mark77-DE/Smart-Filament-Sample-Board/screenshots/halter-3d.png

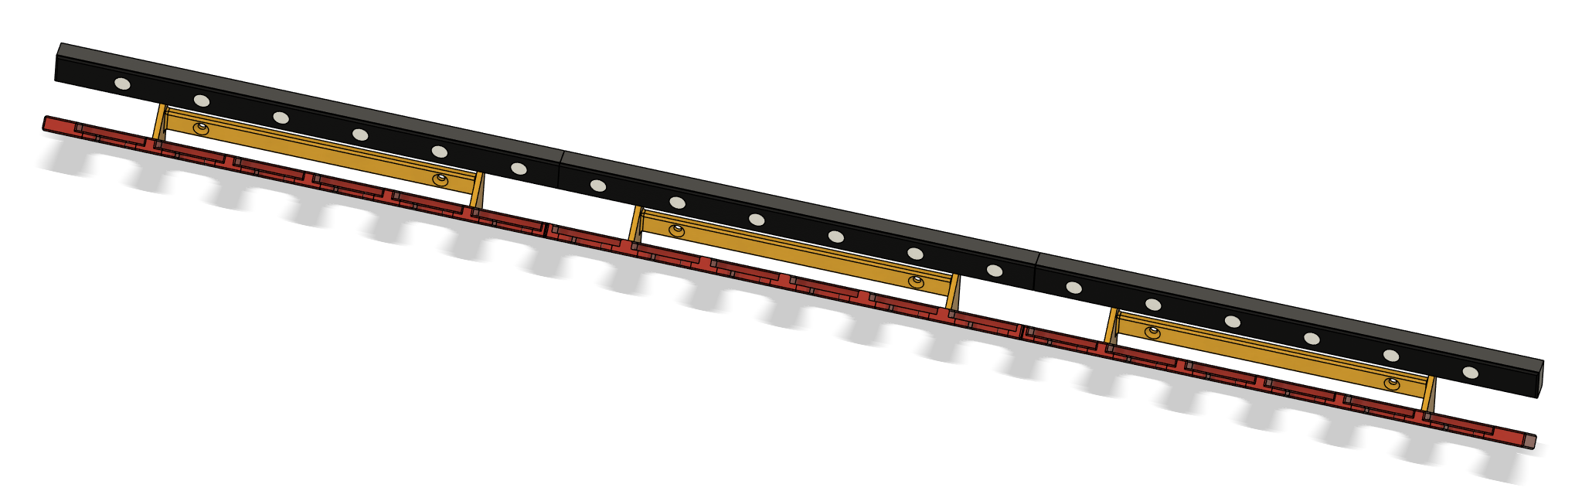
screenshots/halter-3d.png
