mark77-DE/Smart-Filament-Sample-Board/screenshots/samplefuss.png

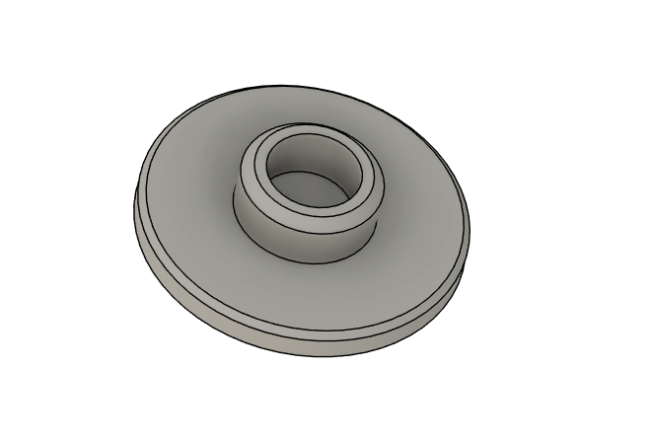
screenshots/samplefuss.png
