mark77-DE/Smart-Filament-Sample-Board/screenshots/settings_button.png

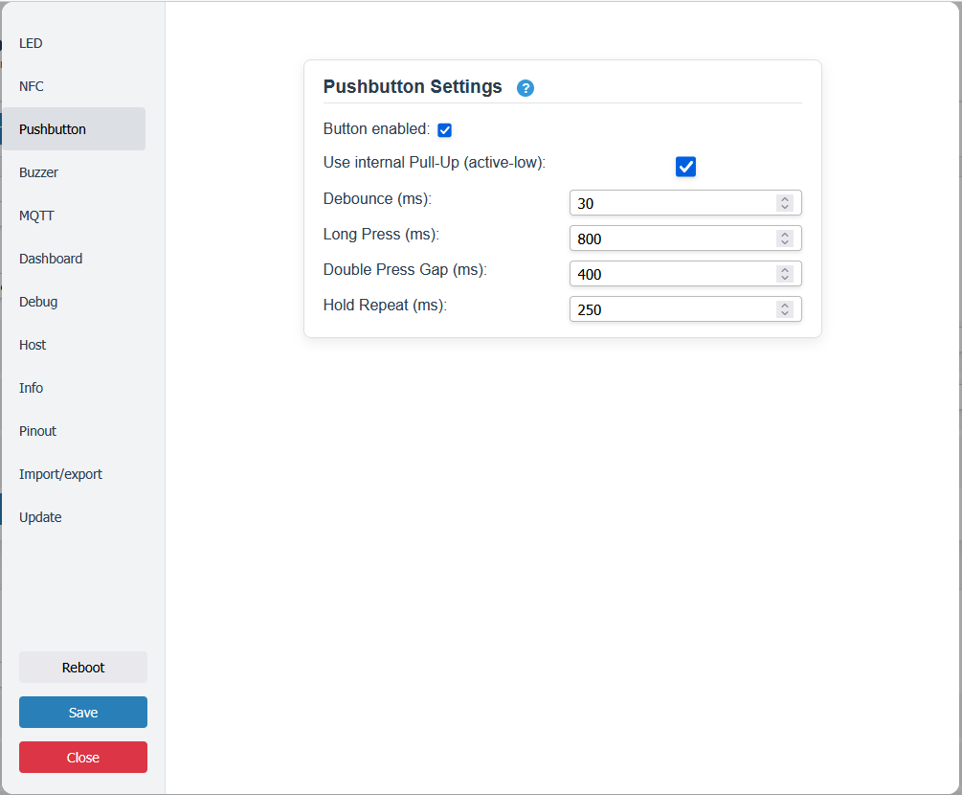
screenshots/settings_button.png
