mark77-DE/Smart-Filament-Sample-Board/screenshots/settings_dashboard.png

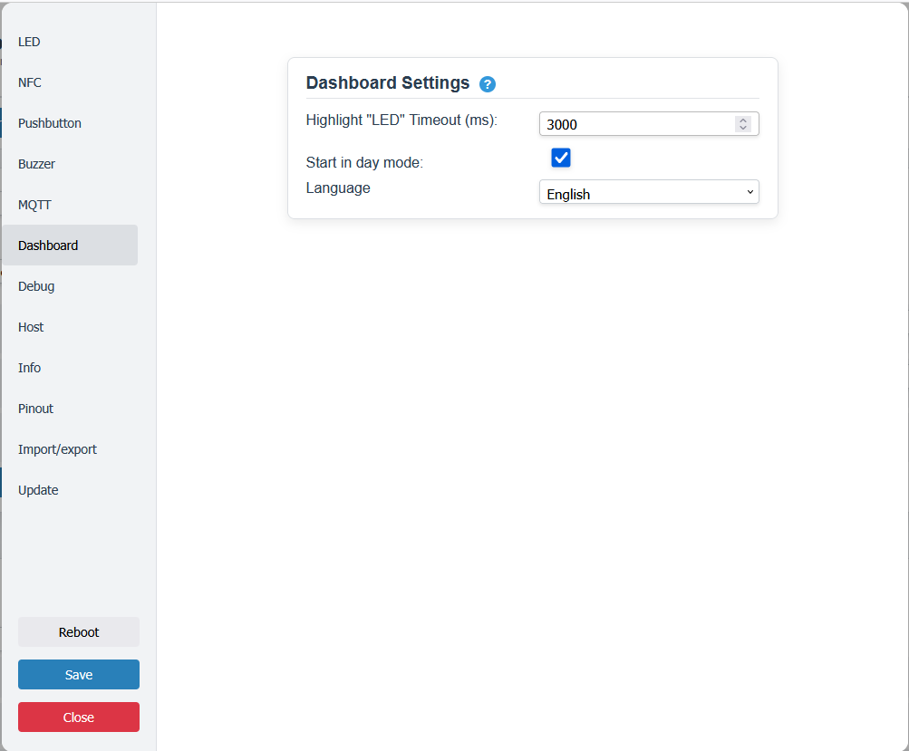
screenshots/settings_dashboard.png
