mark77-DE/Smart-Filament-Sample-Board/screenshots/settings_host.png

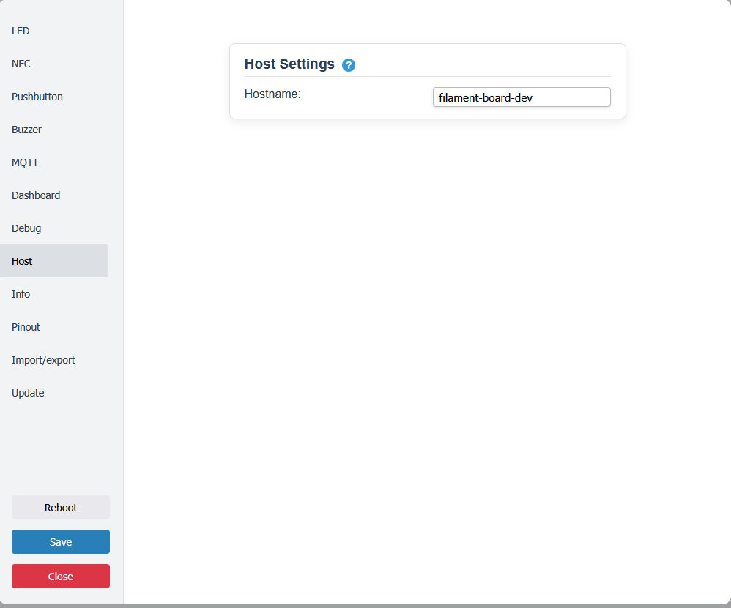
screenshots/settings_host.png
