mark77-DE/Smart-Filament-Sample-Board/screenshots/settings_import-export.png

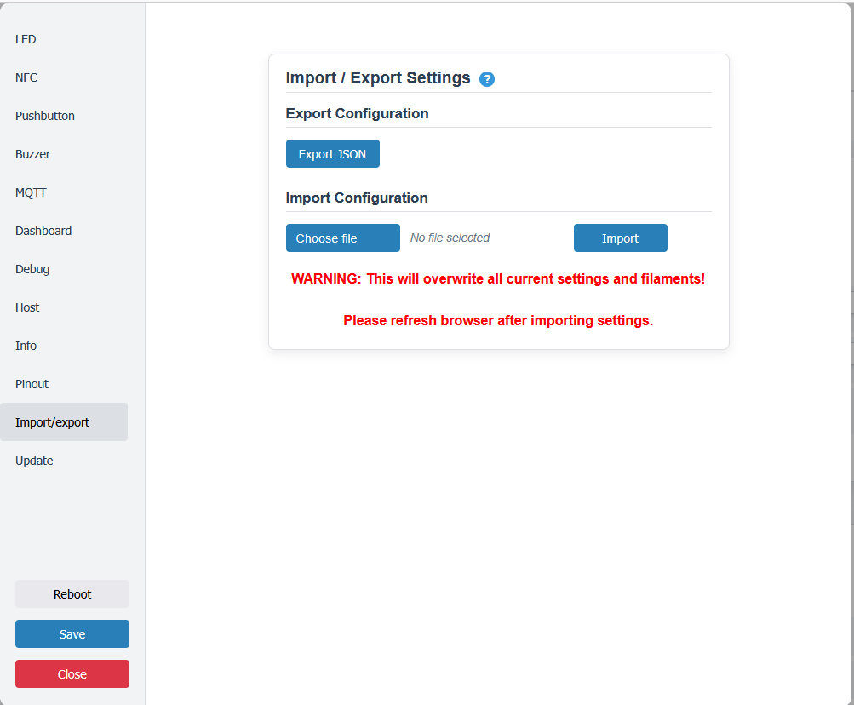
screenshots/settings_import-export.png
