mark77-DE/Smart-Filament-Sample-Board/screenshots/settings_info-1.png

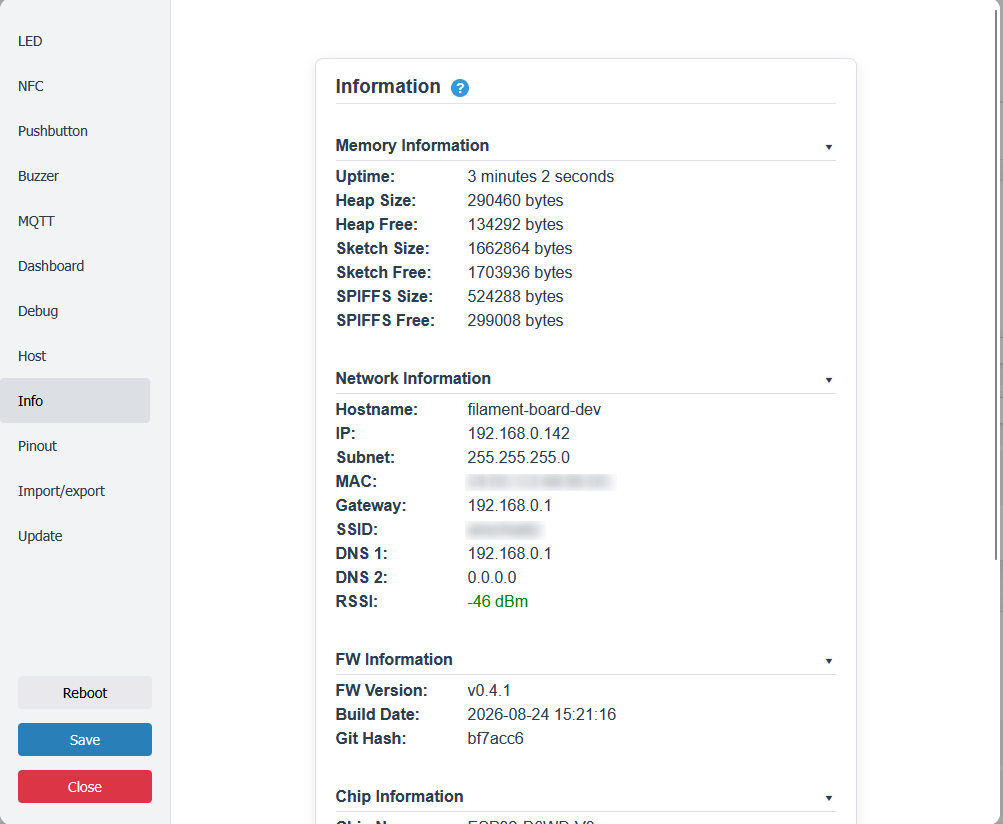
screenshots/settings_info-1.png
