mark77-DE/Smart-Filament-Sample-Board/screenshots/settings_main.png

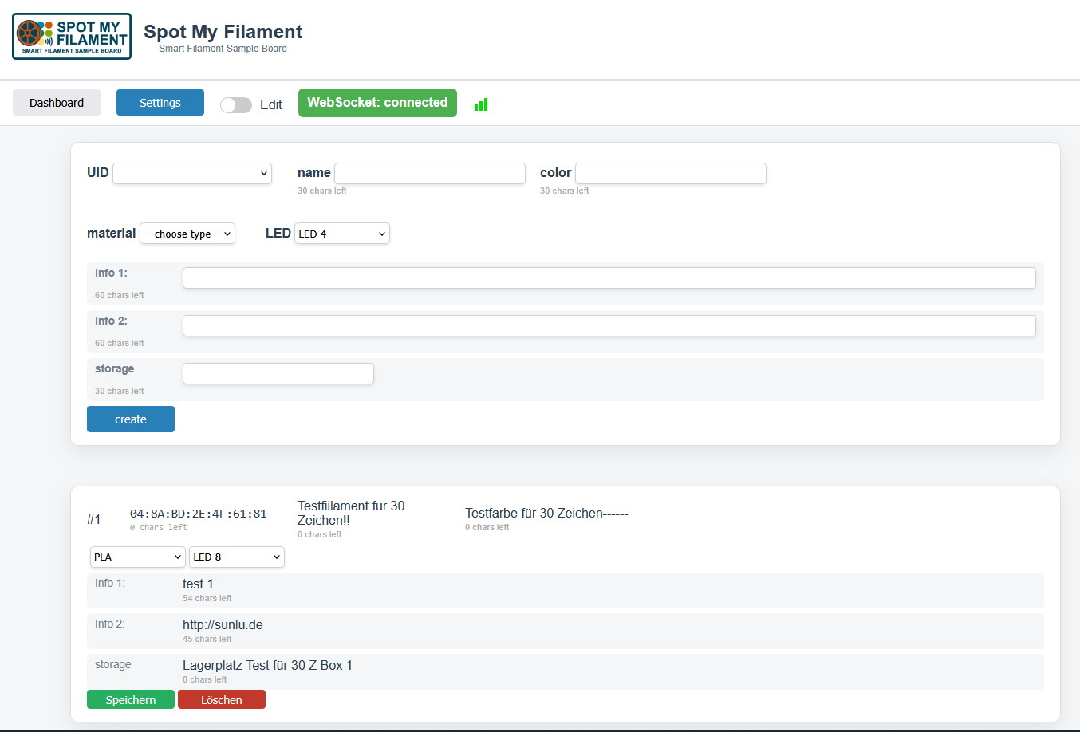
screenshots/settings_main.png
