mark77-DE/Smart-Filament-Sample-Board/screenshots/settings_main_led.png

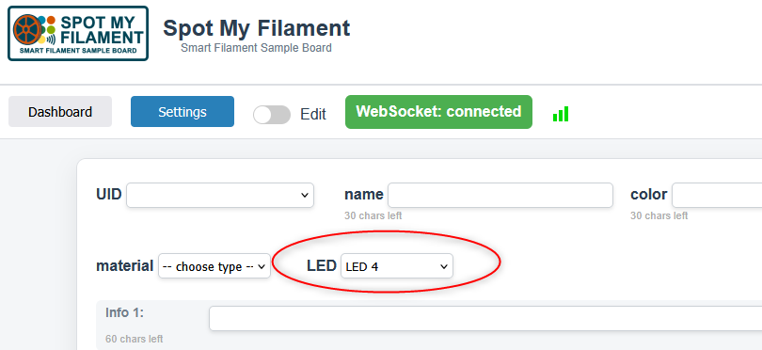
screenshots/settings_main_led.png
