mark77-DE/Smart-Filament-Sample-Board/screenshots/settings_update.png

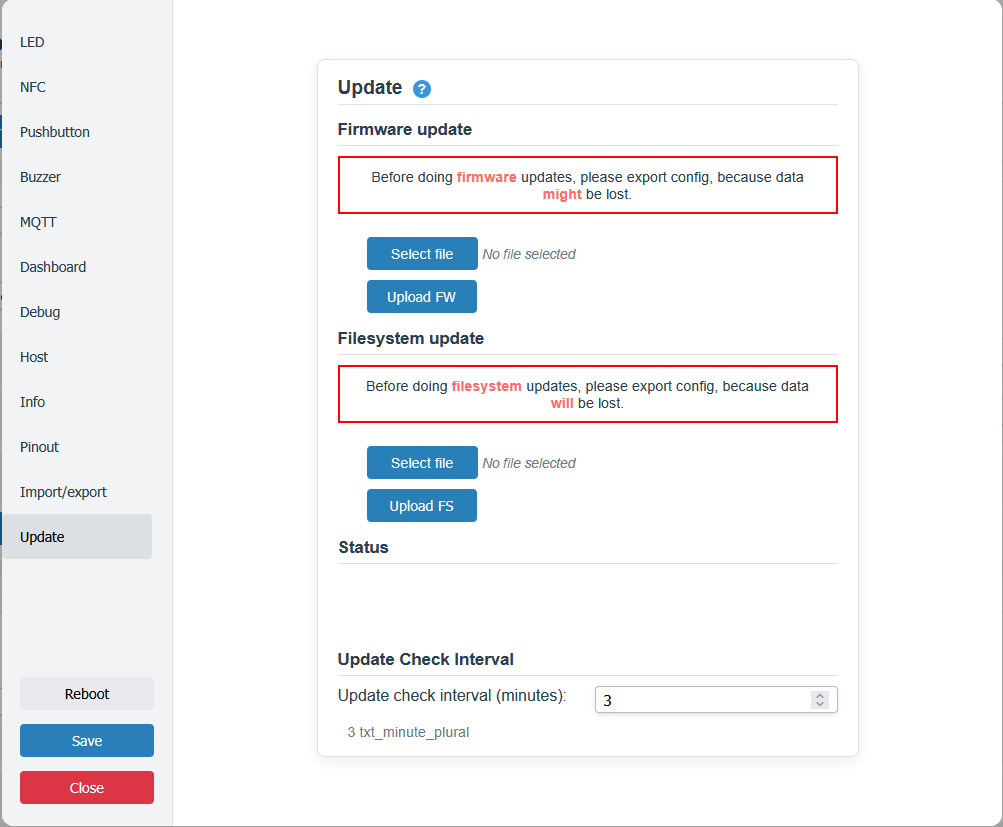
screenshots/settings_update.png
