mark77-DE/Smart-Filament-Sample-Board/3D-Daten/CDU/CDU_Kolja_V3_Wandhalterung_Schrauben.stl

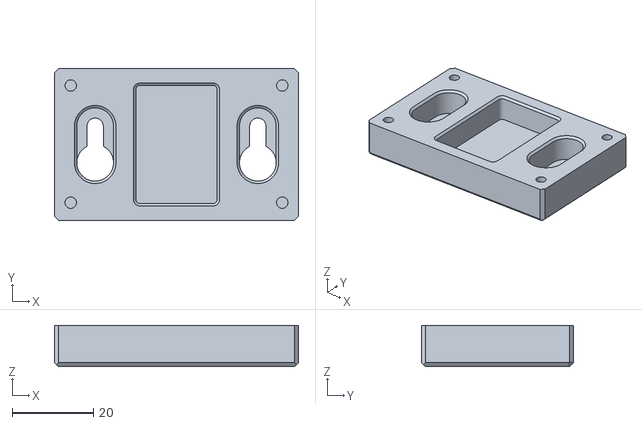
[picture p35: CAD file, 2025-12-17]
3D-Daten/CDU/CDU_Kolja_V3_Wandhalterung_Schrauben.stl
60.0 x 37.3 x 10.2
