mark77-DE/Smart-Filament-Sample-Board/3D-Daten/Printfiles/Filament-Sample-Board_6x.3mf

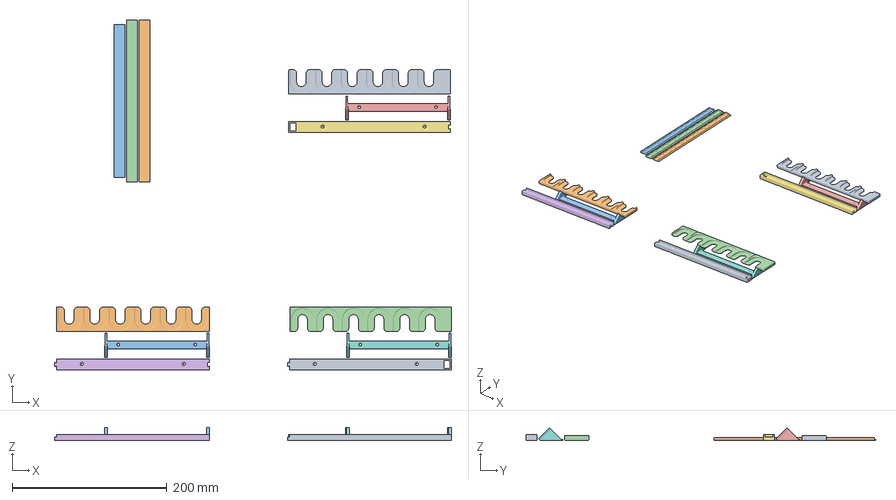
[picture p36: CAD file, 2026-08-30]
3D-Daten/Printfiles/Filament-Sample-Board_6x.3mf
513.6 x 452.6 x 16.2 mm
Sample-Mount_left
Sample-Mount_middle
Wall-mount_middle
Sample-Mount_right
Wall-mount_left
LED-Mount_middle
LED-Mount_left
Wall-mount_right
LED-Mount_right
Left
Middle
Right
