mark77-DE/Smart-Filament-Sample-Board/3D-Daten/CAD-Komponenten/ESP32-C3.step

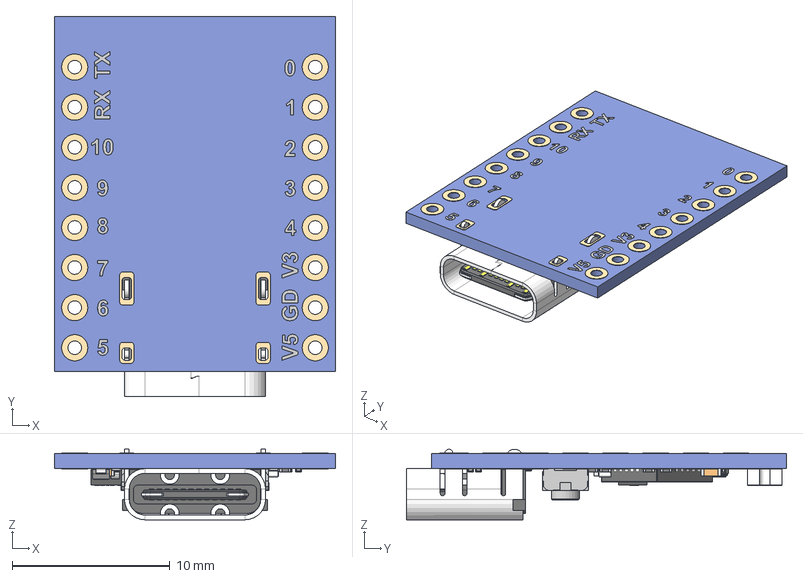
[picture p38: CAD file, 2025-12-13]
3D-Daten/CAD-Komponenten/ESP32-C3.step
17.8 x 24.1 x 4.47 mm
