mark77-DE/Smart-Filament-Sample-Board/3D-Daten/CDU/CDU_Kolja_V3_WAGO_Cover_Mounting_Plate.3mf

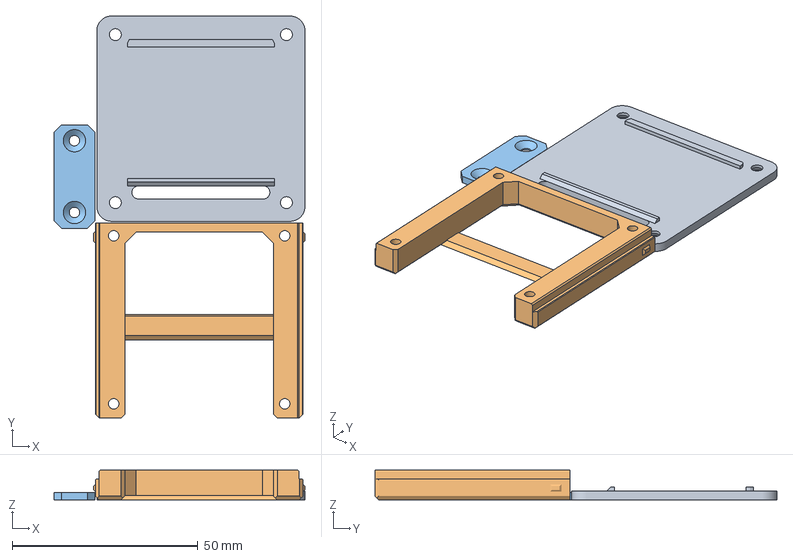
[picture p39: CAD file, 2025-12-17]
3D-Daten/CDU/CDU_Kolja_V3_WAGO_Cover_Mounting_Plate.3mf
67.5 x 108.1 x 8.00 mm
CDU_Kolja_V3_WAGO_Cover_Mounting_Plate.stl
CDU_Kolja_V3_WAGO_Slide_Rail.stl
CDU_Kolja_V3_USB_Cover.stl
