mark77-DE/Smart-Filament-Sample-Board/3D-Daten/Printfiles/Filament-Sample-Board_7x.3mf

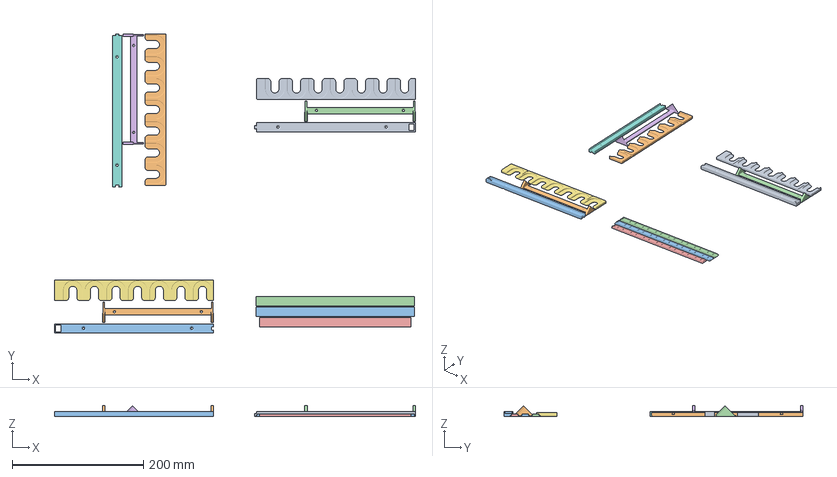
[picture p40: CAD file, 2026-08-30]
3D-Daten/Printfiles/Filament-Sample-Board_7x.3mf
550.7 x 456.6 x 16.2 mm
Sample-Mount_right
Sample-Mount_middle
LED-Cover_left
Wall-Mount_right
LED-Cover_middle
Wall-mount_middle
Sample-Mount_left
LED-Mount_middle
LED-Mount_right
Wall-Mount_left
LED-Mount_left
LED-Cover_right
