mark77-DE/Smart-Filament-Sample-Board/3D-Daten/CAD-Daten_Halter/Alte Version/FilamentSampleRegal v10.step

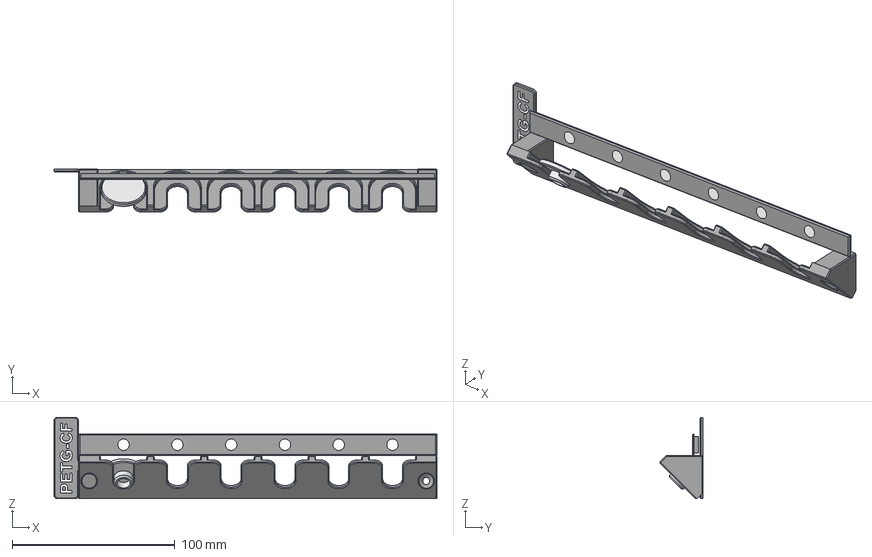
[picture p41: CAD file, 2025-12-06]
3D-Daten/CAD-Daten_Halter/Alte Version/FilamentSampleRegal v10.step
235.0 x 26.4 x 50.0 mm
Halter
LED-Halter-Deckel
SampleFuss
Schild
SchraubenKappe
