mark77-DE/Smart-Filament-Sample-Board/3D-Daten/CAD-Komponenten/OLED 2.42 V1.1 SSD1309.STEP

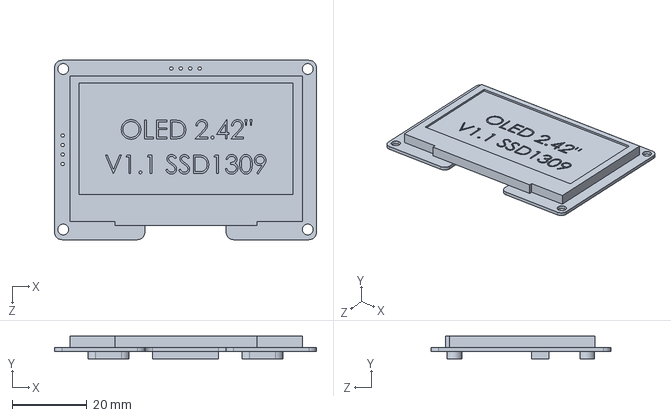
[picture p42: CAD file, 2025-12-13]
3D-Daten/CAD-Komponenten/OLED 2.42 V1.1 SSD1309.STEP
70.2 x 6.10 x 48.1 mm
