mark77-DE/Smart-Filament-Sample-Board/3D-Daten/CDU/CDU_Kolja_V3_NFC_Einsatz.3mf

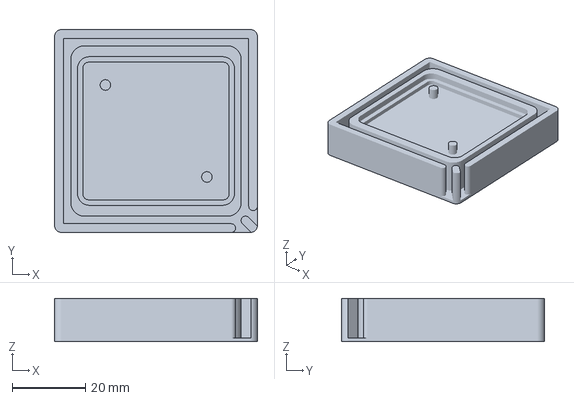
[picture p43: CAD file, 2025-12-17]
3D-Daten/CDU/CDU_Kolja_V3_NFC_Einsatz.3mf
55.6 x 55.6 x 11.8 mm
