mark77-DE/Smart-Filament-Sample-Board/3D-Daten/CAD-Daten_Halter/Alte Version/Halter.step

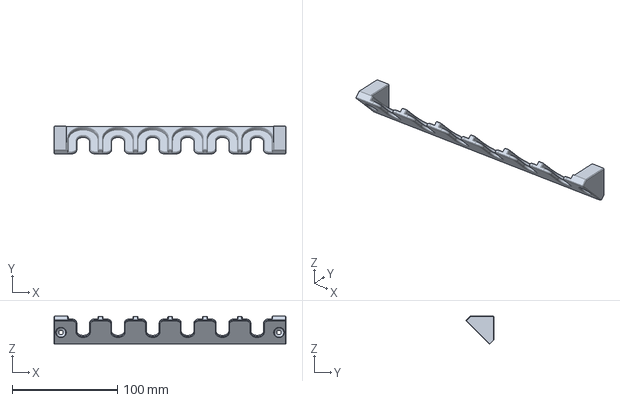
[picture p44: CAD file, 2025-12-06]
3D-Daten/CAD-Daten_Halter/Alte Version/Halter.step
220.0 x 26.4 x 26.4 mm
