mark77-DE/Smart-Filament-Sample-Board/3D-Daten/CAD-Komponenten/221-2411.stp

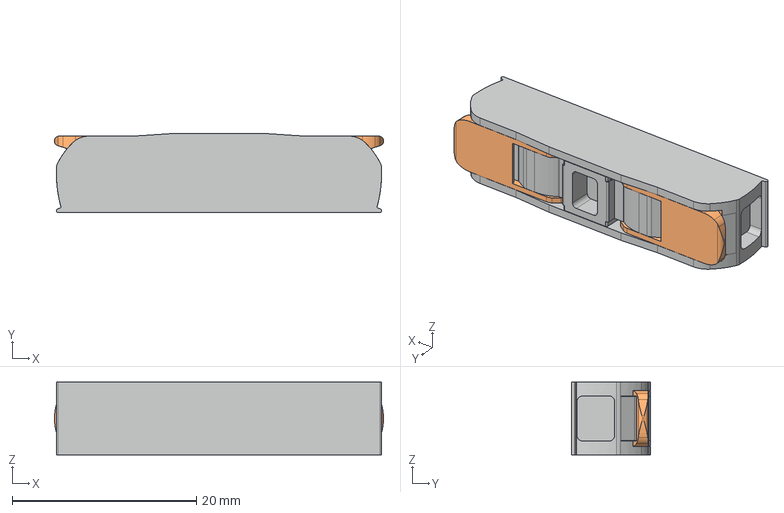
[picture p45: CAD file, 2025-12-13]
3D-Daten/CAD-Komponenten/221-2411.stp
35.7 x 8.60 x 7.90 mm
