mark77-DE/Smart-Filament-Sample-Board/3D-Daten/CDU/CDU_Kolja_V3_Final_Frontplatte.stp

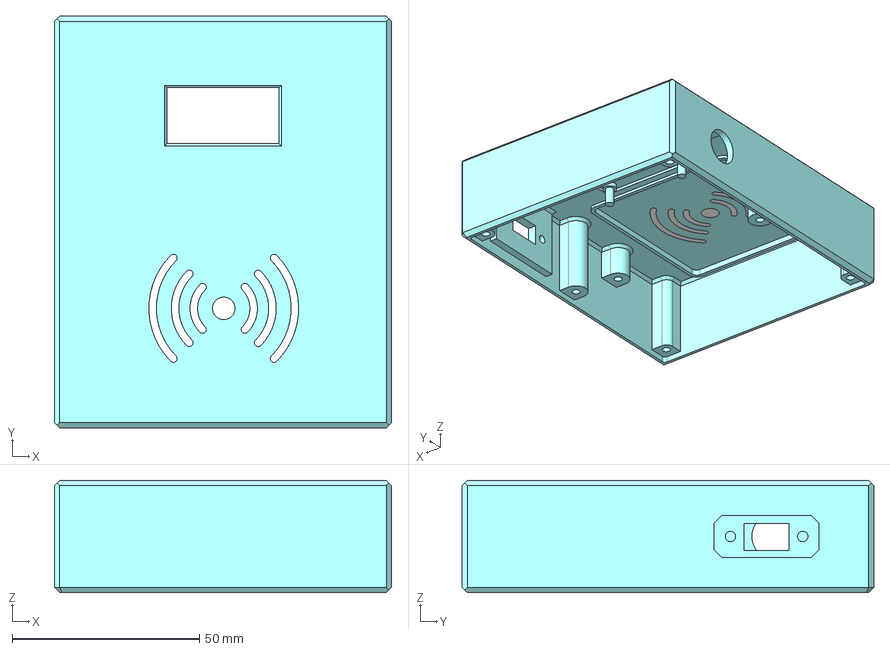
[picture p46: CAD file, 2025-12-17]
3D-Daten/CDU/CDU_Kolja_V3_Final_Frontplatte.stp
90.0 x 110.0 x 30.0 mm
Frontplatte
NFC_Symbol
