mark77-DE/Smart-Filament-Sample-Board/3D-Daten/CAD-Daten_Halter/Alte Version/SampleFuss.step

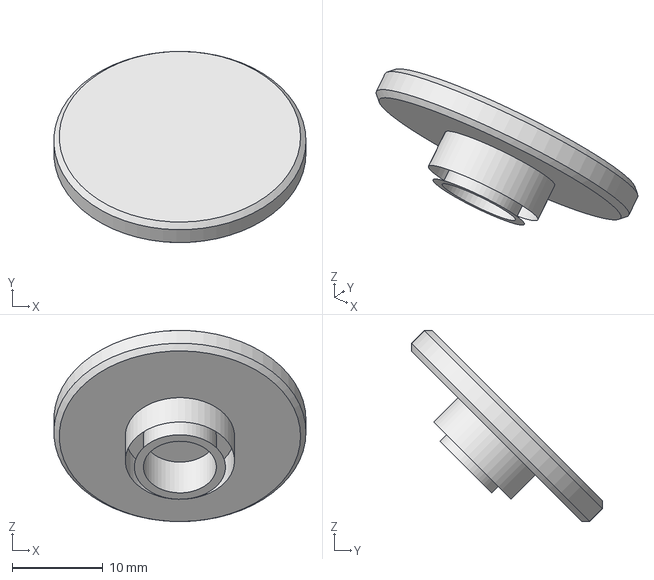
[picture p47: CAD file, 2025-12-06]
3D-Daten/CAD-Daten_Halter/Alte Version/SampleFuss.step
27.8 x 21.1 x 21.1 mm
