mark77-DE/Smart-Filament-Sample-Board/3D-Daten/CAD-Komponenten/Adafruit_NeoPixel_Stick_8.step

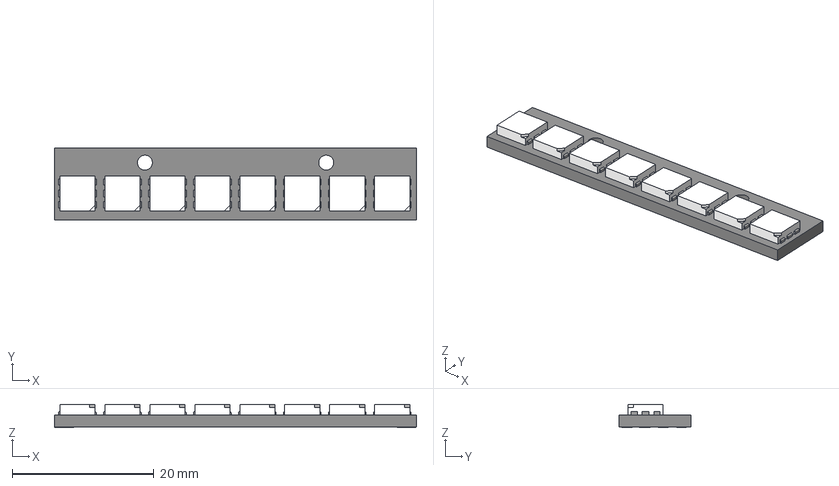
[picture p48: CAD file, 2025-12-13]
3D-Daten/CAD-Komponenten/Adafruit_NeoPixel_Stick_8.step
51.1 x 10.2 x 3.27 mm
NeoPixel Stick - 8 x WS2812 5050 RGB LED v2
LED - SMD RGB (WS2812) x 8
Solder Pads
