mark77-DE/Smart-Filament-Sample-Board/3D-Daten/CDU/CDU_Kolja_V3_Final_ESP32_Plate.stp

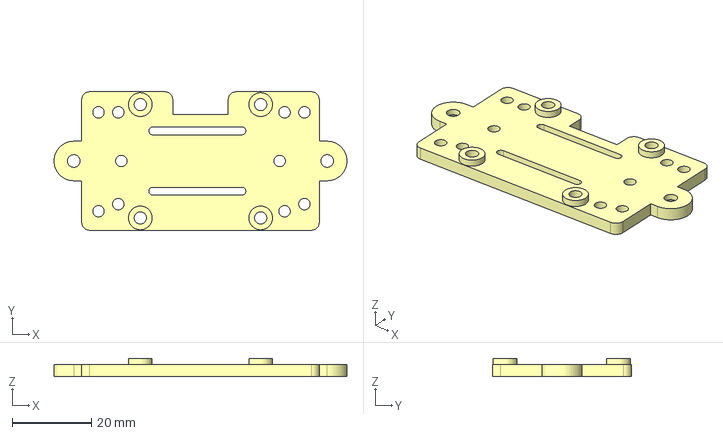
[picture p49: CAD file, 2025-12-17]
3D-Daten/CDU/CDU_Kolja_V3_Final_ESP32_Plate.stp
74.0 x 35.0 x 4.60 mm
ESP_Schrift
ESP_Platte
