mark77-DE/Smart-Filament-Sample-Board/3D-Daten/CAD-Komponenten/OLED13_IIC.stp

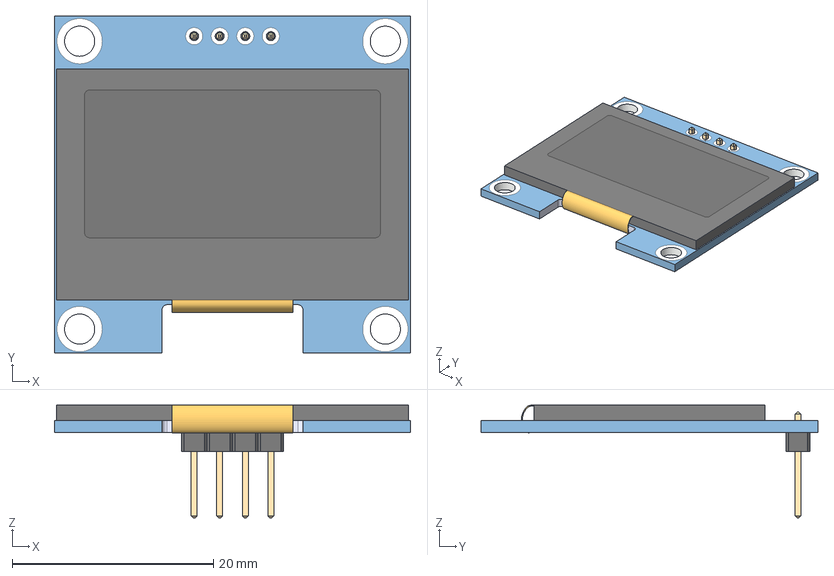
[picture p50: CAD file, 2025-12-13]
3D-Daten/CAD-Komponenten/OLED13_IIC.stp
35.4 x 33.5 x 11.2 mm
