mark77-DE/Smart-Filament-Sample-Board/3D-Daten/CDU/CDU_Kolja_V3_WAGO_Slide_Rail.stl

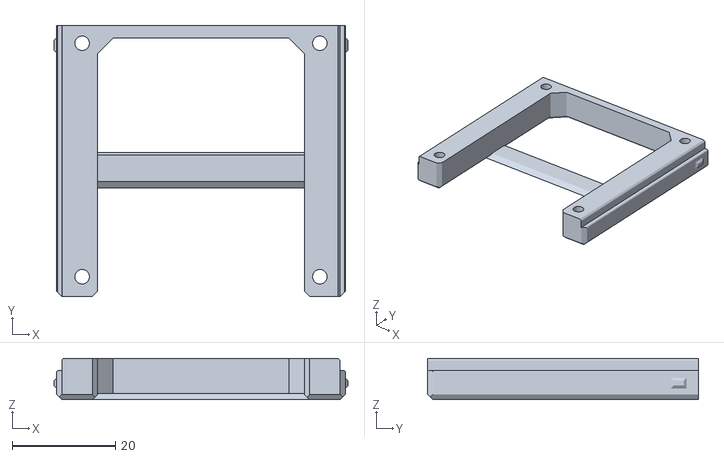
[picture p51: CAD file, 2025-12-17]
3D-Daten/CDU/CDU_Kolja_V3_WAGO_Slide_Rail.stl
56.9 x 52.4 x 8.00
