mark77-DE/Smart-Filament-Sample-Board/3D-Daten/CAD-Daten_Halter/Alte Version/Schild_PLA.step

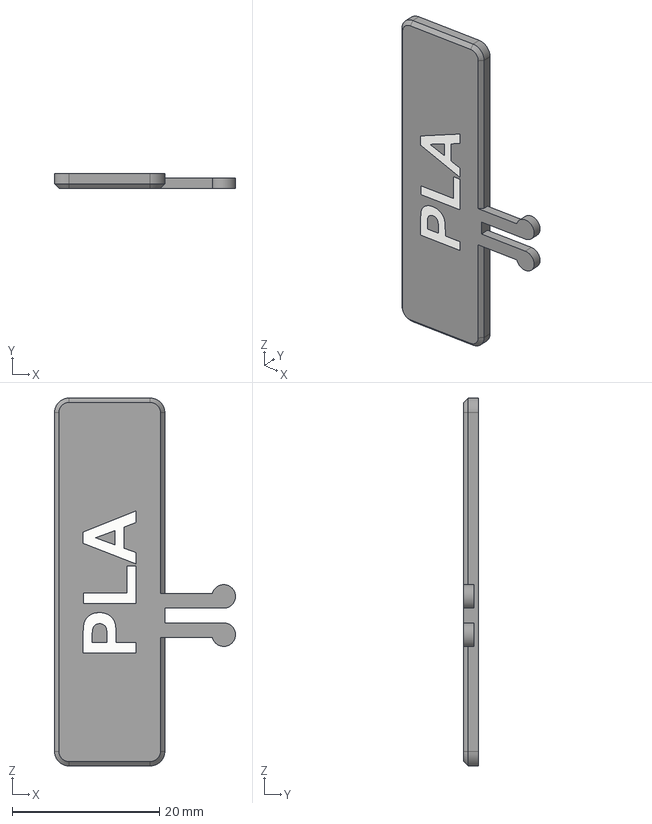
[picture p52: CAD file, 2025-12-06]
3D-Daten/CAD-Daten_Halter/Alte Version/Schild_PLA.step
24.6 x 2.00 x 50.0 mm
