mark77-DE/Smart-Filament-Sample-Board/ESP32-Webserver/src/display/oled/display_anim.cpp

#include "display/display_config.h"

#if DISPLAY_TYPE == DISPLAY_TYPE_SH1106

#include "display/display_anim.h"
#include "display/display.h"
#include "gpio_hardware.h"


// Diese Werte stammen aus dem Animator-Export:
#define FRAME_WIDTH  64
#define FRAME_HEIGHT 64

// Animation
const byte PROGMEM frames[][512] = {
  {0,0,0,0,0,0,0,0,0,0,0,0,0,0,0,0,0,0,0,0,0,0,0,0,0,0,0,0,0,0,0,0,0,0,0,0,0,0,0,0,0,0,0,0,0,0,0,0,0,0,0,0,0,0,0,0,0,0,0,0,0,0,0,0,0,0,0,0,0,0,0,0,0,0,0,0,0,0,0,0,0,0,0,0,0,0,0,0,0,0,0,0,0,0,0,0,0,0,0,24,0,0,0,0,0,0,0,24,0,0,0,0,0,0,0,60,0,0,0,0,0,0,0,60,0,0,0,0,0,0,0,60,0,0,0,0,0,0,0,60,0,0,0,0,0,0,0,60,0,0,0,0,0,0,0,124,0,0,0,0,0,0,0,126,0,0,0,0,0,0,0,110,0,0,0,0,0,0,0,102,0,0,0,0,0,0,0,230,0,0,0,0,0,0,0,230,0,0,0,0,0,0,0,230,0,0,0,0,0,1,192,199,0,96,0,0,0,1,192,199,0,112,0,0,0,3,225,195,0,240,0,0,0,3,225,195,0,248,0,0,0,7,225,131,0,248,0,0,0,7,113,131,1,216,0,0,0,14,115,131,129,220,0,0,7,254,51,131,129,156,31,224,15,252,59,129,131,140,63,240,7,248,63,1,131,142,127,224,0,0,31,1,131,142,96,0,0,0,31,1,131,7,224,0,0,0,15,1,199,7,192,0,0,0,14,1,199,3,192,0,0,0,14,0,198,3,128,0,0,0,6,0,206,1,0,0,0,0,0,0,206,0,0,0,0,0,0,0,204,0,0,0,0,0,0,0,252,0,0,0,0,0,0,0,252,0,0,0,0,0,0,0,120,0,0,0,0,0,0,0,120,0,0,0,0,0,0,0,120,0,0,0,0,0,0,0,112,0,0,0,0,0,0,0,112,0,0,0,0,0,0,0,112,0,0,0,0,0,0,0,0,0,0,0,0,0,0,0,0,0,0,0,0,0,0,0,0,0,0,0,0,0,0,0,0,0,0,0,0,0,0,0,0,0,0,0,0,0,0,0,0,0,0,0,0,0,0,0,0,0,0,0,0,0,0,0,0,0,0,0,0,0,0,0,0,0,0,0,0,0,0,0,0,0,0,0,0,0,0,0,0,0,0,0,0,0,0,0,0,0,0,0},
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

enum IdleState {
    IDLE_OFF,
    IDLE_ANIM,
    IDLE_TEXT
};

IdleState     s_state          = IDLE_OFF;
uint16_t      s_frame          = 0;
unsigned long s_lastFrameTime  = 0;
unsigned long s_textStartTime  = 0;

// --- Textanimation ---
static const uint8_t MAX_IDLE_TEXT_LEN = 32;

char           s_textBuffer[MAX_IDLE_TEXT_LEN + 1] = {0};
uint8_t        s_textLen         = 0;
uint8_t        s_textCharIndex   = 0;
unsigned long  s_lastCharTime    = 0;

// --- Cursoranimation ---
bool           s_cursorVisible   = false;
unsigned long  s_lastCursorBlink = 0;

// --- Cursor layout (so only the cursor needs to be drawn) ---
bool           s_layoutReady     = false;
int16_t        s_textX           = 0;
int16_t        s_textY           = 0;
uint16_t       s_textW           = 0;
uint16_t       s_textH           = 0;

int16_t        s_cursorX         = 0;
int16_t        s_cursorY         = 0;
uint16_t       s_cursorW         = 0;
uint16_t       s_cursorH         = 0;

static int16_t s_cursorX1 = 0;   // x-offset aus getTextBounds
static int16_t s_cursorY1 = 0;   // y-offset aus getTextBounds

// ------------------------------------------------------------
// Frame cropping for 32px
// ------------------------------------------------------------

static void drawFrameCropped(DisplayType &display, uint16_t frameIdx) {
    // 1bpp Bitmap: bytes pro Zeile
    const int16_t bytesPerRow = (FRAME_WIDTH + 7) / 8;

    // Target height = min(FRAME_HEIGHT, SCREEN_HEIGHT)
    int16_t drawH = FRAME_HEIGHT;
    if (SCREEN_HEIGHT < FRAME_HEIGHT) drawH = SCREEN_HEIGHT;

    // Vertikal mittig aus dem 64px Frame ausschneiden
    int16_t srcYOffset = 0;
        if (drawH < FRAME_HEIGHT) {
        #if FRAME_CROP_MODE_CENTER
            srcYOffset = (FRAME_HEIGHT - drawH) / 2;
        #else
        srcYOffset = 0; // oben abschneiden
        #endif
}


    const uint8_t* bmp = &frames[frameIdx][0];
    bmp += srcYOffset * bytesPerRow; // vertikal „croppen“

    int16_t x = (SCREEN_WIDTH  - FRAME_WIDTH) / 2;
    int16_t y = (SCREEN_HEIGHT - drawH)      / 2;
    if (x < 0) x = 0;
    if (y < 0) y = 0;

    displayClear();
    display.drawBitmap(x, y, bmp, FRAME_WIDTH, drawH, DISPLAY_COLOR);
    displayFlush();
}


// ------------------------------------------------------------
// Reset animation
// ------------------------------------------------------------
static void resetTextAnimation(unsigned long now) {
    const char *src = IDLE_TEXT_STRING;
    size_t len = strlen(src);
    if (len > MAX_IDLE_TEXT_LEN) len = MAX_IDLE_TEXT_LEN;

    memcpy(s_textBuffer, src, len);
    s_textBuffer[len] = '\0';

    s_textLen         = len;
    s_textCharIndex   = 0;
    s_lastCharTime    = 0;

    s_cursorVisible   = false;
    s_lastCursorBlink = 0;

    s_textStartTime   = now;

    s_layoutReady     = false;   // Layout will be calculated later
}


// ------------------------------------------------------------
// Helper: draw centered text (for typing phase)
// (still clears the display, but only while typing)
// ------------------------------------------------------------
static void drawIdleText(DisplayType &display, uint8_t count, bool showCursor) {
    if (count == 0) {
        displayClear();
        displayFlush();
        return;
    }

    if (count > s_textLen)
        count = s_textLen;

    char tmp[MAX_IDLE_TEXT_LEN + 2];

    memcpy(tmp, s_textBuffer, count);
    uint8_t len = count;

    if (showCursor && count == s_textLen) {
        tmp[len++] = '_';
    }

    tmp[len] = '\0';

    int16_t x1, y1;
    uint16_t w, h;

    displayClear();
    display.setTextWrap(false);
    display.setTextColor(DISPLAY_COLOR);

    display.getTextBounds(tmp, 0, 0, &x1, &y1, &w, &h);

    int16_t x = (SCREEN_WIDTH  - (int16_t)w) / 2 - x1;
    int16_t y = (SCREEN_HEIGHT - (int16_t)h) / 2 - y1;

    if (x < 0) x = 0;
    if (y < 0) y = 0;

    display.setCursor(x, y);
    display.print(tmp);
    displayFlush();
}


// ------------------------------------------------------------
// Calculate layout for text + cursor (without clearing anything)
// ------------------------------------------------------------
static void computeLayout(DisplayType &display) {
    if (s_layoutReady || s_textLen == 0) return;

    int16_t x1, y1;
    uint16_t wText, hText;


    // Nur den finalen Text vermessen
    display.getTextBounds(s_textBuffer, 0, 0, &x1, &y1, &wText, &hText);

    int16_t x = (SCREEN_WIDTH  - (int16_t)wText) / 2 - x1;
    int16_t y = (SCREEN_HEIGHT - (int16_t)hText) / 2 - y1;

    if (x < 0) x = 0;
    if (y < 0) y = 0;

    s_textX = x;
    s_textY = y;
    s_textW = wText;
    s_textH = hText;

    // Determine cursor width/height
    int16_t cx1, cy1;
    uint16_t cw, ch;
    display.getTextBounds("_", 0, 0, &cx1, &cy1, &cw, &ch);

    s_cursorX1 = cx1;
    s_cursorY1 = cy1;

    // Cursor zentriert auf neuer Zeile unter dem Text
    s_cursorX = (SCREEN_WIDTH - cw) / 2;
    s_cursorY = s_textY + s_textH + 4;   // +4 als Abstand nach unten

    // Clamp, damit Cursor immer im sichtbaren Bereich bleibt
    if (s_cursorY + (int16_t)ch > SCREEN_HEIGHT) {
        s_cursorY = SCREEN_HEIGHT - (int16_t)ch;
    }
    if (s_cursorY < 0) s_cursorY = 0;

    s_cursorW = cw;
    s_cursorH = ch;

    s_layoutReady = true;
}


// ------------------------------------------------------------
// Draw/erase only the cursor (no clearDisplay!)
// ------------------------------------------------------------
static void drawCursor(DisplayType &display, bool visible) {
    if (!s_layoutReady) return;

    // Clear the cursor area
    display.fillRect(s_cursorX, s_cursorY, s_cursorW, s_cursorH, 0);

    if (visible) {
        display.setTextWrap(false);
        display.setTextColor(DISPLAY_COLOR);

        // ✅ Baseline-Korrektur (DAS war der Bug!)
        display.setCursor(
            s_cursorX - s_cursorX1,
            s_cursorY - s_cursorY1
        );
        display.print("_");
    }

    displayFlush();
}


} // Ende anonymer Namespace




// ============================================================
// PUBLIC API – NAMESPACE DisplayAnim
// ============================================================

namespace DisplayAnim {


// ------------------------------------------------------------
// Start idle normally → animation first
// ------------------------------------------------------------
void startIdle(unsigned long now) {
    s_state         = IDLE_ANIM;
    s_frame         = 0;
    s_lastFrameTime = 0;

    resetTextAnimation(now);
}


// ------------------------------------------------------------
// Start idle with text -> text first (for boot)
// ------------------------------------------------------------
void startIdleTextFirst(unsigned long now) {
    s_state         = IDLE_TEXT;
    s_frame         = 0;
    s_lastFrameTime = 0;

    resetTextAnimation(now);
}


// ------------------------------------------------------------
// Idle stoppen
// ------------------------------------------------------------
void stop() {
    s_state = IDLE_OFF;
}



// ------------------------------------------------------------
// Haupt-Statemachine
// ------------------------------------------------------------
void tickIdle(DisplayType &display, unsigned long now) {

    switch (s_state) {

        // --------------------------
        case IDLE_OFF:
            return;


        // --------------------------
        case IDLE_ANIM: {
            if (s_lastFrameTime == 0 || (now - s_lastFrameTime) >= IDLE_ANIM_FRAME_DELAY) {

                drawFrameCropped(display, s_frame);

                s_lastFrameTime = now;
                s_frame++;

                if (s_frame >= FRAME_COUNT) {
                    s_state = IDLE_TEXT;
                    resetTextAnimation(now);
                }
            }
        } break;


        // --------------------------
        case IDLE_TEXT: {

            // ===== Typewriter animation (character by character) =====
            if (s_textCharIndex < s_textLen) {

                if (s_lastCharTime == 0) {
                    // first character
                    s_textCharIndex = 1;
                    s_lastCharTime  = now;
                    drawIdleText(display, s_textCharIndex, false);
                }
                else if ((now - s_lastCharTime) >= IDLE_TEXT_CHAR_DELAY) {
                    // Next character
                    s_textCharIndex++;
                    s_lastCharTime = now;
                    drawIdleText(display, s_textCharIndex, false);
                }

                // Layout is needed only when the text is finished
            }

            // ===== Cursor-Blinken, nachdem der Text komplett ist =====
            else {
                // Einmal Layout berechnen (Position von Text & Cursor)
                if (!s_layoutReady) {
                    computeLayout(display);
                    s_cursorVisible   = false;
                    s_lastCursorBlink = now;
                    // Text steht bereits vom letzten drawIdleText()
                }

                if ((now - s_lastCursorBlink) >= IDLE_TEXT_CURSOR_BLINK_INTERVAL) {
                    s_cursorVisible   = !s_cursorVisible;
                    s_lastCursorBlink = now;
                    drawCursor(display, s_cursorVisible);
                }
            }

            // ===== Total duration expired? → return to animation =====
            if ((now - s_textStartTime) >= IDLE_TEXT_DURATION) {
                s_state         = IDLE_ANIM;
                s_frame         = 0;
                s_lastFrameTime = 0;
            }

        } break;

    }
}


// ----------------------------------------------
// 3-line typewriter including backward erasing
// ----------------------------------------------
namespace {

// small helper like in display.cpp
static String fixUmlauts_local(String s) {
    s.replace("ä","ae"); s.replace("ö","oe"); s.replace("ü","ue");
    s.replace("Ä","Ae"); s.replace("Ö","Oe"); s.replace("Ü","Ue");
    s.replace("ß","ss");
    return s;
}

// Draw a centered text snippet at the specified line top
static void drawCenteredSubstringAtTop(
    DisplayType& display,
    const String& full,
    size_t count,
    int16_t yTop
) {
    String s = fixUmlauts_local(full.substring(0, count));
    int16_t x1, y1; uint16_t w, h;
    display.getTextBounds(s, 0, 0, &x1, &y1, &w, &h);
    int16_t x = (int16_t)((SCREEN_WIDTH - (int16_t)w) / 2) - x1;
    int16_t y = (int16_t)(yTop - y1); // yTop ist die "Top"-Kante der Zeile
    display.setCursor(x, y);
    display.print(s);
}

// Layout: determine stable Y top positions for the 3 lines,
// so nothing jitters vertically while typing/deleting.
static void computeThreeLineLayout(
    DisplayType& display,
    int16_t& yTop1,
    int16_t& yTop2,
    int16_t& yTop3
) {
    // Font setzen wie im restlichen UI
    display.setTextWrap(false);
    display.setTextColor(DISPLAY_COLOR);
    display.setTextSize(1);
    display.setFont(DISPLAY_FONT); // darf nullptr sein -> Standardfont

    // Measure reference height (stable)
    int16_t rx1, ry1; uint16_t rw, rh;
    display.getTextBounds("Hg", 0, 0, &rx1, &ry1, &rw, &rh);
    int16_t lineHeight = (int16_t)rh + 2;

    // Total block height (3 lines)
    int16_t totalH = (int16_t)(3 * lineHeight);

    // Choose the top start so the block is vertically centered
    int16_t blockTop = (int16_t)((SCREEN_HEIGHT - totalH) / 2);

    yTop1 = blockTop;
    yTop2 = (int16_t)(blockTop + lineHeight);
    yTop3 = (int16_t)(blockTop + 2 * lineHeight);
}

static inline void delay_with_yield(uint32_t ms) {
    uint32_t until = millis() + ms;
    while ((int32_t)(millis() - until) < 0) { yield(); }
}

} // anonymous namespace


// String-Overload: eigentliche Logik
void playThreeLineTypewriter(
    DisplayType& display,
    const String& line1,
    const String& line2,
    const String& line3,
    uint32_t charDelayMs,
    uint32_t linePauseMs,
    uint32_t endHoldMs,
    bool     eraseBackwards,
    uint32_t eraseCharDelayMs,
    uint32_t eraseLinePauseMs
) {
    // Fix for umlauts (as used in the UI)
    String L1 = fixUmlauts_local(line1);
    String L2 = fixUmlauts_local(line2);
    String L3 = fixUmlauts_local(line3);

    // Stabiles Layout (Y-Positionen)
    int16_t yTop1, yTop2, yTop3;
    computeThreeLineLayout(display, yTop1, yTop2, yTop3);

    auto drawAll = [&](size_t c1, size_t c2, size_t c3) {
        displayClear();
        if (c1) drawCenteredSubstringAtTop(display, L1, c1, yTop1);
        if (c2) drawCenteredSubstringAtTop(display, L2, c2, yTop2);
        if (c3) drawCenteredSubstringAtTop(display, L3, c3, yTop3);
        displayFlush();
    };

    // 1) Type line 1
    for (size_t i = 1; i <= L1.length(); ++i) {
        drawAll(i, 0, 0);
        delay_with_yield(charDelayMs);
    }
    delay_with_yield(linePauseMs);

    // 2) Type line 2
    for (size_t i = 1; i <= L2.length(); ++i) {
        drawAll(L1.length(), i, 0);
        delay_with_yield(charDelayMs);
    }
    delay_with_yield(linePauseMs);

    // 3) Type line 3
    for (size_t i = 1; i <= L3.length(); ++i) {
        drawAll(L1.length(), L2.length(), i);
        delay_with_yield(charDelayMs);
    }

    // 4) Hold the full display briefly
    delay_with_yield(endHoldMs);

    if (!eraseBackwards) {
        return; // Finish without backward animation
    }

    // 5) Delete backwards: line 3 → 2 → 1
    delay_with_yield(eraseLinePauseMs);
    for (int i = (int)L3.length() - 1; i >= 0; --i) {
        drawAll(L1.length(), L2.length(), (size_t)i);
        delay_with_yield(eraseCharDelayMs);
    }

    delay_with_yield(eraseLinePauseMs);
    for (int i = (int)L2.length() - 1; i >= 0; --i) {
        drawAll(L1.length(), (size_t)i, 0);
        delay_with_yield(eraseCharDelayMs);
    }

    delay_with_yield(eraseLinePauseMs);
    for (int i = (int)L1.length() - 1; i >= 0; --i) {
        drawAll((size_t)i, 0, 0);
        delay_with_yield(eraseCharDelayMs);
    }

    // End: display stays empty (or you deliberately leave the final image visible here)
    displayClear();
    displayFlush();
}


// PROGMEM-Overload: wandelt um und delegiert
void playThreeLineTypewriter(
    DisplayType& display,
    const __FlashStringHelper* line1,
    const __FlashStringHelper* line2,
    const __FlashStringHelper* line3,
    uint32_t charDelayMs,
    uint32_t linePauseMs,
    uint32_t endHoldMs,
    bool     eraseBackwards,
    uint32_t eraseCharDelayMs,
    uint32_t eraseLinePauseMs
) {
    String s1(line1), s2(line2), s3(line3);
    DisplayAnim::playThreeLineTypewriter(
        display, s1, s2, s3,
        charDelayMs, linePauseMs, endHoldMs,
        eraseBackwards, eraseCharDelayMs, eraseLinePauseMs
    );
}


} // namespace DisplayAnim


#endif
