mark77-DE/Smart-Filament-Sample-Board/ESP32-Webserver/src/display/oled/display_oled.cpp

//display_oled.cpp

#include "display/display_config.h"

#ifndef DISPLAY_TYPE
#define DISPLAY_TYPE DISPLAY_TYPE_SH1106
#endif

#if DISPLAY_TYPE == DISPLAY_TYPE_SH1106

#include "display/display.h"

#include <Arduino.h>
#include "globals.h"
#include "version_info.h"
#include "config.h"
#include "pins.h"
#include "update_manager.h"
#include "display/display_anim.h"


DisplayType* MYDISPLAY::_display = nullptr;

static const int STD_FONT_HEIGHT = 7;

DisplayType display(SCREEN_WIDTH, SCREEN_HEIGHT, &Wire, OLED_RESET_PIN);


void displayInit()
{
    if(CONFIGV2.system.debugMode)
    {
        Serial.printf("[DISPLAY] Wire.begin SDA=%d SCL=%d\n", SDA_PIN, SCL_PIN);
    }

    bool wireOk = Wire.begin(SDA_PIN, SCL_PIN);

    if(CONFIGV2.system.debugMode)
    {
        Serial.printf("[DISPLAY] Wire.begin result: %s\n",
                      wireOk ? "OK" : "FAILED");
    }
    

    if (!initDisplay(display)) {
        Serial.println("Display init failed");
        return;
    }

    if(CONFIGV2.system.debugMode)
    {
        Serial.println("[DISPLAY] Display init OK");
    }

    display.clearDisplay();

    MYDISPLAY::init(&display);
}






void displayClear()
{
    display.clearDisplay();
}

void displayFlush()
{
    display.display();
}

// ------------------------------------------------------------
// Umlauts → ASCII
// ------------------------------------------------------------
static String fixUmlauts(String s) {
  s.replace("ä", "ae"); s.replace("ö", "oe"); s.replace("ü", "ue");
  s.replace("Ä", "Ae"); s.replace("Ö", "Oe"); s.replace("Ü", "Ue");
  s.replace("ß", "ss");
  return s;
}

// ------------------------------------------------------------
// Auto-fit for a single horizontally centered line.
// Supports 32px displays (standard font) and 64px displays with DISPLAY_FONT.
// yBaselineOrTop: bei 32px = top (wir addieren STD_FONT_HEIGHT), bei 64px = baseline.
// lineHeight: distributed line height (for 64px: derived from DISPLAY_FONT)
// ------------------------------------------------------------
static void printLineAutoFitCenteredGfx(DisplayType* d, const String& raw,
                                        int16_t yBaselineOrTop,
                                        bool smallDisplay, int16_t lineHeight, const GFXfont* font = DISPLAY_FONT)
{
  if (!d) return;

  String t = fixUmlauts(raw);
  int16_t x1, y1; uint16_t w, h;

  if (smallDisplay) {
    // Always use the standard font, yBaseline = yTop + STD_FONT_HEIGHT
    d->setFont(nullptr);
    d->setTextSize(1);
    int16_t yBase = yBaselineOrTop + STD_FONT_HEIGHT;

    d->getTextBounds(t, 0, 0, &x1, &y1, &w, &h);
    if (w <= SCREEN_WIDTH) {
      int16_t x = (SCREEN_WIDTH - (int16_t)w)/2 - x1;
      d->setCursor(x, yBase);
      d->print(t);
      return;
    }
    // Truncate + "..."
    String base = t, out;
    while (base.length() > 0) {
      out = base + "...";
      d->getTextBounds(out, 0, 0, &x1, &y1, &w, &h);
      if (w <= SCREEN_WIDTH) {
        int16_t x = (SCREEN_WIDTH - (int16_t)w)/2 - x1;
        d->setCursor(x, yBase);
        d->print(out);
        return;
      }
      base.remove(base.length()-1);
    }
    d->setCursor((SCREEN_WIDTH-9)/2, yBase);
    d->print("...");
    return;
  }

  // 64px: try DISPLAY_FONT first
  bool useStd = false;
  if (font != nullptr) {
    d->setFont(font);
    d->setTextSize(1);
    d->getTextBounds(t, 0, 0, &x1, &y1, &w, &h);
    if (w > SCREEN_WIDTH) useStd = true;
  } else {
    useStd = true;
  }

  if (useStd) {
    d->setFont(nullptr);
    d->setTextSize(1);
    // Center the standard-font baseline visually within the line height
    int16_t yBase = yBaselineOrTop - (lineHeight - STD_FONT_HEIGHT)/2;

    d->getTextBounds(t, 0, 0, &x1, &y1, &w, &h);
    if (w <= SCREEN_WIDTH) {
      int16_t x = (SCREEN_WIDTH - (int16_t)w)/2 - x1;
      d->setCursor(x, yBase);
      d->print(t);
      return;
    }
    String base = t, out;
    while (base.length() > 0) {
      out = base + "...";
      d->getTextBounds(out, 0, 0, &x1, &y1, &w, &h);
      if (w <= SCREEN_WIDTH) {
        int16_t x = (SCREEN_WIDTH - (int16_t)w)/2 - x1;
        d->setCursor(x, yBase);
        d->print(out);
        return;
      }
      base.remove(base.length()-1);
    }
    d->setCursor((SCREEN_WIDTH-9)/2, yBase);
    d->print("...");
    return;
  }

  // DISPLAY_FONT passt
  d->getTextBounds(t, 0, 0, &x1, &y1, &w, &h);
  {
    int16_t x = (SCREEN_WIDTH - (int16_t)w)/2 - x1;
    d->setCursor(x, yBaselineOrTop);
    d->print(t);
  }
}

// ------------------------------------------------------------
// Display the 3 lines: vendor / type / color (original, unchanged)
// ------------------------------------------------------------
void MYDISPLAY::show(const FilamentEntry& entry) {
  if (!_display) return;

  _display->clearDisplay();
  _display->setTextWrap(false);
  _display->setTextColor(DISPLAY_COLOR);

  const bool smallDisplay = (SCREEN_HEIGHT <= 32);

  // Determine line height
  int16_t x1=0, y1=0; uint16_t w=0, h=0;
  int16_t lineHeight = 0;

  if (smallDisplay) {
    lineHeight = STD_FONT_HEIGHT + 2;
  } else {
    _display->setFont(DISPLAY_FONT);
    _display->setTextSize(1);
    _display->getTextBounds("Hg", 0, 0, &x1, &y1, &w, &h);
    lineHeight = (int16_t)h + 2;
  }

  // Start-Y
  int16_t y = smallDisplay ? 0 : lineHeight;

  // Helper function: one left-aligned line (original logic)
  auto printLineAutoFit = [&](const String& rawText, int16_t yLine) {
    String t = fixUmlauts(rawText);

    if (smallDisplay) {
      _display->setFont(nullptr);
      _display->setTextSize(1);
      int16_t yBase = yLine + STD_FONT_HEIGHT;

      _display->getTextBounds(t, 0, 0, &x1, &y1, &w, &h);
      if (w <= SCREEN_WIDTH) {
        _display->setCursor(0, yBase);
        _display->print(t);
        return;
      }
      String base = t;
      String out;
      while (base.length() > 0) {
        out = base + "...";
        _display->getTextBounds(out, 0, 0, &x1, &y1, &w, &h);
        if (w <= SCREEN_WIDTH) {
          _display->setCursor(0, yBase);
          _display->print(out);
          return;
        }
        base.remove(base.length()-1);
      }
      _display->setCursor(0, yBase);
      _display->print("...");
      return;
    }

    bool forceFallback = (DISPLAY_AUTOFIT_THRESHOLD > 0 && t.length() > DISPLAY_AUTOFIT_THRESHOLD);

    if (DISPLAY_FONT != nullptr && !forceFallback) {
      _display->setFont(DISPLAY_FONT);
      _display->setTextSize(1);
      _display->getTextBounds(t, 0, 0, &x1, &y1, &w, &h);
      if (w <= SCREEN_WIDTH) {
        _display->setCursor(0, yLine);
        _display->print(t);
        return;
      }
    }

    _display->setFont(nullptr);
    _display->setTextSize(1);
    int16_t yAdjusted = yLine - (lineHeight - STD_FONT_HEIGHT)/2;

    _display->getTextBounds(t, 0, 0, &x1, &y1, &w, &h);
    if (w <= SCREEN_WIDTH) {
      _display->setCursor(0, yAdjusted);
      _display->print(t);
      return;
    }
    String base = t, out;
    while (base.length() > 0) {
      out = base + "...";
      _display->getTextBounds(out, 0, 0, &x1, &y1, &w, &h);
      if (w <= SCREEN_WIDTH) {
        _display->setCursor(0, yAdjusted);
        _display->print(out);
        return;
      }
      base.remove(base.length()-1);
    }
    _display->setCursor(0, yAdjusted);
    _display->print("...");
  };

  // Ausgabe: vendor / type / color
  printLineAutoFit(entry.vendor, y); y += lineHeight;
  printLineAutoFit(entry.type,   y); y += lineHeight;
  printLineAutoFit(entry.color,  y);

  _display->display();

  // Restore font state
  _display->setFont(DISPLAY_FONT);
  _display->setTextSize(1);

  // Debug
  if (CONFIGV2.system.debugMode) {
    Serial.println();
    Serial.println(F("[DISPLAY] SHOW:"));
    Serial.print(" Vendor: "); Serial.println(entry.vendor);
    Serial.print(" Type:   "); Serial.println(entry.type);
    Serial.print(" Color:  "); Serial.println(entry.color);
  }
  
}

// ------------------------------------------------------------
// One centered line (original function, unchanged)
// ------------------------------------------------------------
void MYDISPLAY::showCentered(const String& msg, const int FOREGROUND_COLOR, const int BACKGROUND_COLOR) {
  if (!_display) return;

  _display->clearDisplay();

  _display->setFont(DISPLAY_FONT);
  _display->setTextSize(1);
  _display->setTextWrap(false);
  _display->setTextColor(DISPLAY_COLOR);

  int16_t x1, y1; uint16_t w, h;
  String fixed = fixUmlauts(msg);
  _display->getTextBounds(fixed, 0, 0, &x1, &y1, &w, &h);

  int16_t x = (SCREEN_WIDTH  - (int16_t)w) / 2 - x1;
  int16_t y = (SCREEN_HEIGHT - (int16_t)h) / 2 - y1;

  _display->setCursor(x, y);
  _display->print(fixed);
  _display->display();
}

// ------------------------------------------------------------
// Two centered lines (existing API explicitly available again)
// ------------------------------------------------------------
void MYDISPLAY::showTwoLinesCentered(const String& line1, const String& line2) {
  if (!_display) return;

  _display->clearDisplay();
  _display->setTextWrap(false);
  _display->setTextColor(DISPLAY_COLOR);

  const bool smallDisplay = (SCREEN_HEIGHT <= 32);

  // Determine line height
  int16_t x1=0, y1=0; uint16_t w=0, h=0;
  int16_t lineHeight = 0;
  if (smallDisplay) {
    lineHeight = STD_FONT_HEIGHT + 2;
  } else {
    _display->setFont(DISPLAY_FONT);
    _display->setTextSize(1);
    _display->getTextBounds("Hg", 0, 0, &x1, &y1, &w, &h);
    lineHeight = (int16_t)h + 2;
  }

  // Aim: distribute vertically over 2 lines → start at the top (same as show)
  int16_t y = smallDisplay ? 0 : lineHeight;

  printLineAutoFitCenteredGfx(_display, line1, y, smallDisplay, lineHeight); y += lineHeight;
  printLineAutoFitCenteredGfx(_display, line2, y, smallDisplay, lineHeight);

  _display->display();

  _display->setFont(DISPLAY_FONT);
  _display->setTextSize(1);
}

// ------------------------------------------------------------
// Three centered lines (new - for reboot/countdown/prompts)
// ------------------------------------------------------------
void MYDISPLAY::showThreeLinesCentered(const String& line1, const String& line2, const String& line3, int foregroundColor, int backgroundColor) {
  if (!_display) return;

  _display->clearDisplay();
  _display->setTextWrap(false);
  _display->setTextColor(DISPLAY_COLOR);

  const bool smallDisplay = (SCREEN_HEIGHT <= 32);

  // Determine line height
  int16_t x1=0, y1=0; uint16_t w=0, h=0;
  int16_t lineHeight = 0;
  if (smallDisplay) {
    lineHeight = STD_FONT_HEIGHT + 2;
  } else {
    _display->setFont(DISPLAY_FONT);
    _display->setTextSize(1);
    _display->getTextBounds("Hg", 0, 0, &x1, &y1, &w, &h);
    lineHeight = (int16_t)h + 2;
  }

  // Start at the top (32px) or with spacing (64px) – consistent with show()
  int16_t y = smallDisplay ? 0 : lineHeight;

  printLineAutoFitCenteredGfx(_display, line1, y, smallDisplay, lineHeight); y += lineHeight;
  printLineAutoFitCenteredGfx(_display, line2, y, smallDisplay, lineHeight); y += lineHeight;
  printLineAutoFitCenteredGfx(_display, line3, y, smallDisplay, lineHeight);

  _display->display();

  _display->setFont(DISPLAY_FONT);
  _display->setTextSize(1);
}

// ------------------------------------------------------------
// Three centered lines (new - for reboot/countdown/prompts)
// ------------------------------------------------------------
void MYDISPLAY::showFourLinesCentered(const String& line1, const String& line2, const String& line3, const String& line4) {
  if (!_display) return;

  _display->clearDisplay();
  _display->setTextWrap(false);
  _display->setTextColor(DISPLAY_COLOR);

  const bool smallDisplay = (SCREEN_HEIGHT <= 32);

  // Determine line height
  int16_t x1=0, y1=0; uint16_t w=0, h=0;
  int16_t lineHeight = 0;
  if (smallDisplay) {
    lineHeight = STD_FONT_HEIGHT + 2;
  } else {
    _display->setFont(&FreeMono7pt7b);
    _display->setTextSize(1);
    _display->getTextBounds("Hg", 0, 0, &x1, &y1, &w, &h);
    lineHeight = (int16_t)h + 3;
  }

  // Start at the top (32px) or with spacing (64px) – consistent with show()
  int16_t y = smallDisplay ? 0 : lineHeight;

  printLineAutoFitCenteredGfx(_display, line1, y, smallDisplay, lineHeight, &FreeMono7pt7b); y += lineHeight;
  printLineAutoFitCenteredGfx(_display, line2, y, smallDisplay, lineHeight, &FreeMono7pt7b); y += lineHeight;
  printLineAutoFitCenteredGfx(_display, line3, y, smallDisplay, lineHeight, &FreeMono7pt7b); y += lineHeight;
  printLineAutoFitCenteredGfx(_display, line4, y, smallDisplay, lineHeight, &FreeMono7pt7b);

  _display->display();

  _display->setFont(DISPLAY_FONT);
  _display->setTextSize(1);
}



// --- Neu: Bootscreen 
void MYDISPLAY::showBootVersion(const char* version, const char* dateShort) {
    if (!_display) return;

    String l1 = F("Firmware");
    String l2 = String(version);   // e.g. "FW v0.1.0"
    String l3 = String(dateShort);            // e.g. "21.12:25"

    showThreeLinesCentered(l1, l2, l3);            
}


void MYDISPLAY::showErrorCentered(const String& msg, const int FOREGROUND_COLOR, const int BACKGROUND_COLOR) {


  showCentered(msg, FOREGROUND_COLOR, BACKGROUND_COLOR);


}


void MYDISPLAY::clear() {
  if (_display) {
    _display->clearDisplay();
    _display->display();
  }
}


namespace {
    bool          s_selfUpdateActive   = false;
    bool          s_finishedShown      = false;
    bool          s_finishedHandled    = false;   // NEU: verhindert Re-Trigger
    unsigned long s_finishedAt         = 0;

    uint8_t       s_lastProgress       = 255;
    String        s_lastMessage        = "";
}

static const unsigned long SELF_UPDATE_RESULT_HOLD_MS = 10000;

void MYDISPLAY::renderSelfUpdateStatus(const SelfUpdateStatus& status) {

    // New update run detected (running set back to true) -> reset everything
    if (status.running) {
        s_finishedHandled = false;
    }

    // No update active, no pending completion -> nothing to do
    if (!status.running && (!status.finished || s_finishedHandled)) {
        s_selfUpdateActive = false;
        s_finishedShown    = false;
        return;
    }

    if (!s_selfUpdateActive) {
        DisplayAnim::stop();
        s_selfUpdateActive = true;
        s_lastProgress = 255;
        s_lastMessage  = "";
    }

    // ---- Completion (success/failure) ----
    if (status.finished && !s_finishedHandled) {
        if (!s_finishedShown) {
            if (status.success) {
                showThreeLinesCentered(F("FW update"), F("success"), F("rebooting"));
            } else {
                showTwoLinesCentered(F("FW update"), F("failed"));
            }
            s_finishedShown = true;
            s_finishedAt    = millis();
        }

        if (millis() - s_finishedAt >= SELF_UPDATE_RESULT_HOLD_MS) {
            s_finishedHandled  = true;   // important: this event is now "consumed"
            s_finishedShown    = false;
            s_selfUpdateActive = false;
            DisplayAnim::startIdle(millis());
        }
        return;
    }

    // ---- Still running: show progress ----
    if (status.progress != s_lastProgress || status.message != s_lastMessage) {
        char pct[8];
        snprintf(pct, sizeof(pct), "%u%%", status.progress);
        showThreeLinesCentered(F("FW update"), status.message.c_str(), String(pct));

        s_lastProgress = status.progress;
        s_lastMessage  = status.message;
    }
}




#endif
