mark77-DE/Smart-Filament-Sample-Board/ESP32-Webserver/src/my_webserver.cpp

#include "my_webserver.h"
#include <ArduinoJson.h>
#include <Update.h>
#include <LittleFS.h>
#include "ledctrl_filament.h"
#include "ledctrl_nfc.h"
#include "globals.h"
#include "filament_db.h"
#include "filehandling.h"
#include "version_info.h"
#include "reboot_handler.h"
#include "nfc.h"
#include "gpio_hardware.h"
#include "display/display.h"
#include "display/display_anim.h"
#include "esp_image_format.h"
#include "config.h"
#include "pins.h"
#include "esp_system.h"
#include "update_manager.h"
#include "esp_chip_info.h"
#include <WiFi.h>
#include "web_assets_generated.h"
#include "filaman_manager.h"

File fsFile; // global or outside the lambda in this .cpp

extern void webifArmIdleTimeout(uint32_t ms);

unsigned long lastHeartbeatMs = 0;
const unsigned long HEARTBEAT_INTERVAL_MS = 1000; // 1 Sekunde

// Forward declaration
extern void renderRebootCountdown(unsigned long nowMs);

extern void handleUID(const String &uid, UidSource source);

const char *boardVariant = BOARD_VARIANT;

// --- Chip-ID Mapping (aus esp_app_format.h) ---
enum : uint16_t
{
    IMG_CHIP_ESP32 = 0x0000,
    IMG_CHIP_ESP32S2 = 0x0002,
    IMG_CHIP_ESP32C3 = 0x0005,
    IMG_CHIP_ESP32S3 = 0x0009,
    IMG_CHIP_ESP32C2 = 0x000C,
    IMG_CHIP_ESP32C6 = 0x000D,
    IMG_CHIP_ESP32H2 = 0x0010,
};

String chipIdToName(uint16_t id)
{
    switch (id)
    {
    case IMG_CHIP_ESP32:
        return "ESP32";
    case IMG_CHIP_ESP32S2:
        return "ESP32-S2";
    case IMG_CHIP_ESP32C3:
        return "ESP32-C3";
    case IMG_CHIP_ESP32S3:
        return "ESP32-S3";
    case IMG_CHIP_ESP32C2:
        return "ESP32-C2";
    case IMG_CHIP_ESP32C6:
        return "ESP32-C6";
    case IMG_CHIP_ESP32H2:
        return "ESP32-H2";
    default:
        return "unbekannt (0x" + String(id, HEX) + ")";
    }
}

uint16_t runningChipId()
{
    esp_chip_info_t info;
    esp_chip_info(&info);
    switch (info.model)
    {
    case CHIP_ESP32:
        return IMG_CHIP_ESP32;
    case CHIP_ESP32S2:
        return IMG_CHIP_ESP32S2;
    case CHIP_ESP32C3:
        return IMG_CHIP_ESP32C3;
    case CHIP_ESP32S3:
        return IMG_CHIP_ESP32S3;
    case CHIP_ESP32C2:
        return IMG_CHIP_ESP32C2;
    case CHIP_ESP32C6:
        return IMG_CHIP_ESP32C6;
    case CHIP_ESP32H2:
        return IMG_CHIP_ESP32H2;
    default:
        return 0xFFFF;
    }
}

static bool otaAborted = false;

SysInfo getSysInfo()
{
    SysInfo info;

    // Enum -> String
    info.chipName = ESP.getChipModel();
    info.cores = ESP.getChipCores();
    info.revision = ESP.getChipRevision();
    info.flashSize = ESP.getFlashChipSize();
    info.fwVersion = FIRMWARE_VERSION;
    info.buildDate = BUILD_DATE_SHORT;

    return info;
}

// ----------------- WebSocket Event -----------------
void onWsEvent(AsyncWebSocket *server, AsyncWebSocketClient *client,
               AwsEventType type, void *arg, uint8_t *data, size_t len)
{
    LEDCTRL_FILAMENT::netBusyHint(350);
    LEDCTRL_NFC::netBusyHint(350);

    if (type != WS_EVT_DATA)
        return;

    AwsFrameInfo *info = (AwsFrameInfo *)arg;
    if (info->opcode != WS_TEXT)
        return;

    // --- FIX: WS-Fragmente zusammensetzen ---
    static String wsBuf;
    if (info->index == 0)
    {
        wsBuf = "";
        wsBuf.reserve(info->len);
    }

    wsBuf.concat((const char *)data, len);

    // Not complete yet?
    if (!(info->final && (info->index + len == info->len)))
    {
        return;
    }

    // wsBuf is complete now
    JsonDocument doc;
    DeserializationError err = deserializeJson(doc, wsBuf);
    if (err)
    {
        if (CONFIGV2.system.debugMode)
        {
            Serial.print("WS JSON parse error: ");
            Serial.println(err.c_str());
            Serial.print("WS raw: ");
            Serial.println(wsBuf);
        }
        return;
    }

    const char *action = doc["action"] | "";
    if (CONFIGV2.system.debugMode)
    {
        Serial.print("WS action: ");
        Serial.println(action);
    }

    if (strcmp(action, "highlightUIDLED") == 0)
    {
        // --- Send ACK immediately back to this client ---
        // (so JS does not spam retries)
        uint32_t seq = doc["seq"] | 0;
        if (seq != 0)
        {
            JsonDocument ack;
            ack["action"] = "ack";
            ack["seq"] = seq;

            String out;
            serializeJson(ack, out);
            client->text(out);
        }

        // ab hier "heavy work"
        String uid = doc["uid"].as<String>();
        uint32_t t = (CONFIGV2.system.webLEDTimeout > 0) ? CONFIGV2.system.webLEDTimeout : (uint32_t)CONFIGV2.led.timeout;

        LEDCTRL_FILAMENT::webifHoldFor((uint16_t)min<uint32_t>(t, 65535));
        webifArmIdleTimeout(t);

        handleUID(uid, UidSource::WEBIF);
    }
    else if (strcmp(action, "highlightMultiLED") == 0)
    {

        // --- Send ACK immediately back to this client ---
        uint32_t seq = doc["seq"] | 0;
        if (seq != 0)
        {
            JsonDocument ack;
            ack["action"] = "ack";
            ack["seq"] = seq;

            String out;
            serializeJson(ack, out);
            client->text(out);
        }

        // --- Determine timeout ---
        uint32_t t = (CONFIGV2.system.webLEDTimeout > 0)
                         ? CONFIGV2.system.webLEDTimeout
                         : (uint32_t)CONFIGV2.led.timeout;

        uint16_t holdMs = (uint16_t)min<uint32_t>(t, 65535);

        LEDCTRL_FILAMENT::webifHoldFor(holdMs);
        webifArmIdleTimeout(t);

        // --- UIDs verarbeiten ---
        JsonArray uids = doc["uids"].as<JsonArray>();

        FilamentEntry entry;
        int16_t index = 0;
        bool anyHit = false;

        LEDCTRL_FILAMENT::allOff();

        for (JsonVariant uidVar : uids)
        {
            String uid = uidVar.as<String>();

            if (CONFIGV2.system.debugMode)
            {
                Serial.print(index++);
                Serial.print(": WS highlightUID: ");
                Serial.println(uid);
            }

            if (FilamentDB::findByUID(uid, entry))
            {
                LEDCTRL_FILAMENT::setPixel(entry.ledIndex, CONFIGV2.led.color);
                anyHit = true;

                if (CONFIGV2.system.debugMode)
                {
                    Serial.printf(
                        "  -> LED %u (%s %s %s | %s | %s | %s)\n",
                        entry.ledIndex,
                        entry.vendor.c_str(),
                        entry.type.c_str(),
                        entry.color.c_str(),
                        entry.info1.c_str(),
                        entry.info2.c_str(),
                        entry.storage.c_str());
                }
            }
            else if (CONFIGV2.system.debugMode)
            {
                Serial.print("  !! UID not found: ");
                Serial.println(uid);
            }
        }

        if (!anyHit && CONFIGV2.system.debugMode)
        {
            Serial.println("WS highlightMultiLED: no matching UIDs");
        }
    }
    else if (strcmp(action, "highlightSingleLed") == 0)
    {

        if (CONFIGV2.system.debugMode)
        {
            Serial.println("WS highlightSingleLed received");
        }

        int ledIndex = doc["led"] | -1; // Default -1, falls key fehlt
        if (ledIndex < 0)
        {
            Serial.println("WS highlightSingleLed: LED index missing or invalid");
            return;
        }

        activateLed(ledIndex);
        uint32_t t = (CONFIGV2.system.webLEDTimeout > 0) ? CONFIGV2.system.webLEDTimeout : (uint32_t)CONFIGV2.led.timeout;

        LEDCTRL_FILAMENT::webifHoldFor((uint16_t)min<uint32_t>(t, 65535));
        webifArmIdleTimeout(t);
    }
}

// Helper: find an embedded asset by filename, nullptr if not found
const WebAsset *findAsset(const char *filename)
{
    for (size_t i = 0; i < WEB_ASSETS_COUNT; i++)
    {
        if (strcmp(WEB_ASSETS[i].filename, filename) == 0)
            return &WEB_ASSETS[i];
    }
    return nullptr;
}

// Registers a route serving one embedded asset, with optional cache-control
void serveAsset(AsyncWebServer &server, const char *urlPath, const char *filename, const char *cacheControl)
{
    const WebAsset *asset = findAsset(filename);
    if (!asset)
    {
        Serial.printf("[web_assets] WARNING: %s not embedded!\n", filename);
        return;
    }
    server.on(urlPath, HTTP_GET, [asset, cacheControl](AsyncWebServerRequest *request)
              {
        AsyncWebServerResponse *response = request->beginResponse(200, asset->mime, asset->data, asset->len);
        if (asset->gzipped) response->addHeader("Content-Encoding", "gzip");
        response->addHeader("Cache-Control", cacheControl);
        request->send(response); });
}

// ------------------ Webserver Init -------------------
void initWebServer(AsyncWebServer &server, AsyncWebSocket &ws)
{

    // LittleFS mounten
    if (!LittleFS.begin(true))
    { // true = format if mount fails
        Serial.println("[LittleFS] mount failed!");
    }
    else
    {
        Serial.println("[LittleFS] mounted successfully!");
        Serial.print("  [LittleFS] Total Bytes: ");
        Serial.println(LittleFS.totalBytes());
        Serial.print("  [LittleFS] Used Bytes:  ");
        Serial.println(LittleFS.usedBytes());
    }

    ws.onEvent(onWsEvent);
    server.addHandler(&ws);

    // Embedded web assets (formerly served via serveStatic from LittleFS)
    serveAsset(server, "/settings", "settings.html", "no-cache");
    serveAsset(server, "/script.js", "script.js", "public, max-age=604800");
    serveAsset(server, "/style.css", "style.css", "public, max-age=604800");
    serveAsset(server, "/settings.js", "settings.js", "public, max-age=604800");
    serveAsset(server, "/settings.css", "settings.css", "public, max-age=604800");
    serveAsset(server, "/logo.png", "logo.png", "public, max-age=2592000");
    serveAsset(server, "/favicon.ico", "favicon.ico", "public, max-age=2592000");
    serveAsset(server, "/update.js", "update.js", "no-cache");
    serveAsset(server, "/lang_de.json", "lang_de.json", "public, max-age=604800");
    serveAsset(server, "/lang_en.json", "lang_en.json", "public, max-age=604800");
    serveAsset(server, "/i18n_help.js", "i18n_help.js", "public, max-age=604800");
    serveAsset(server, "/", "index.html", "no-cache");
    serveAsset(server, "/index.html", "index.html", "no-cache");

    server.on("/api/version", HTTP_GET, [](AsyncWebServerRequest *request)
              {

        SysInfo info = getSysInfo();

        // FIX: network-load hint – build/send JSON
        LEDCTRL_FILAMENT::netBusyHint(250);
        LEDCTRL_NFC::netBusyHint(250);

        JsonDocument doc;
        doc["firmware"]                 = FIRMWARE_VERSION;
        doc["git_hash"]                 = GIT_HASH;
        doc["build_date"]               = BUILD_DATE;
        doc["build_date_short"]         = BUILD_DATE_SHORT;
        doc["display_type"]             = MYDISPLAY::getDisplayVariant();
        doc["update_filename"]          = getFirmwareAssetName();
        doc["latest_firmware_version"]  = LATEST_FIRMWARE_VERSION;
        doc["config_version"]           = CONFIGV2.system.version;
        doc["boardVariant"]             = boardVariant;
        doc["chipName"]                 = info.chipName;
        doc["cores"]                    = info.cores;
        doc["revision"]                 = info.revision;
        doc["flashSize"]                = info.flashSize;
        doc["nfc_available"]            = g_nfcInfo.available;
        doc["nfc_fwVerMajor"]           = g_nfcInfo.fwVerMajor;
        doc["nfc_fwVerMinor"]           = g_nfcInfo.fwVerMinor;
        char chipHex[6]; // enough for 0xFFFF
        sprintf(chipHex, "0x%04X", g_nfcInfo.chipID);
        doc["nfc_chipID"]               = chipHex; // als String
        String mac                      = WiFi.macAddress();
        doc["wifi_mac"]                 = mac;
        doc["hostname"]                 = WiFi.getHostname();
        doc["wifi_ip"]                  = WiFi.localIP().toString();
        doc["wifi_gateway"]             = WiFi.gatewayIP().toString();
        doc["wifi_subnet"]              = WiFi.subnetMask().toString();
        doc["wifi_ssid"]                = WiFi.SSID();
        
        doc["wifi_bssid"]               = WiFi.BSSIDstr();
        doc["wifi_channel"]             = WiFi.channel();
        doc["wifi_dns1"]                = WiFi.dnsIP(0).toString();
        doc["wifi_dns2"]                = WiFi.dnsIP(1).toString();
        doc["uptime_ms"]                = millis();
        doc["heap_size"]                = ESP.getHeapSize();
        
        doc["sketch_size"]              = ESP.getSketchSize();
        doc["free_sketch"]              = ESP.getFreeSketchSpace();
        
        doc["spiffs_size"]              = LittleFS.totalBytes();
        doc["free_spiffs"]              = LittleFS.usedBytes();

        
    

        
        String response;
        serializeJson(doc, response);
        request->send(200, "application/json", response); });

    server.on("/api/pinout", HTTP_GET, [](AsyncWebServerRequest *request)
              {

    // Network-load hint
    LEDCTRL_FILAMENT::netBusyHint(250);
    LEDCTRL_NFC::netBusyHint(250);

    JsonDocument doc;

    // ------------------------------------------------------------
    // Allgemeine Hardware
    // ------------------------------------------------------------

    doc["LED_PIN"]     = LED_PIN;
    doc["NFC_LED_PIN"] = NFC_LED_PIN;
    doc["BTN_PIN"]     = BTN_PIN;
    doc["BUZ_PIN"]     = BUZ_PIN;


    // ------------------------------------------------------------
    // I2C
    // ------------------------------------------------------------

    doc["I2C"]["SDA"] = SDA_PIN;
    doc["I2C"]["SCL"] = SCL_PIN;


    // ------------------------------------------------------------
    // PN532 SPI
    // ------------------------------------------------------------

    doc["PN532"]["SCK"]  = NFC_SPI_SCK;
    doc["PN532"]["MISO"] = NFC_SPI_MISO;
    doc["PN532"]["MOSI"] = NFC_SPI_MOSI;
    doc["PN532"]["CS"]   = NFC_SPI_CS;

        // ------------------------------------------------------------
        // Display
        // ------------------------------------------------------------

#if DISPLAY_TYPE == DISPLAY_TYPE_ST7789

    doc["display"]["type"] = "ST7789";

    doc["display"]["SPI"]["SCK"]  = TFT_SPI_SCK;
    doc["display"]["SPI"]["MOSI"] = TFT_SPI_MOSI;
    doc["display"]["SPI"]["CS"]   = TFT_SPI_CS;
    doc["display"]["SPI"]["DC"]   = TFT_SPI_DC;
    doc["display"]["SPI"]["RST"]  = TFT_SPI_RST;

#elif DISPLAY_TYPE == DISPLAY_TYPE_SH1106

    doc["display"]["type"] = "SH1106";

#else

    doc["display"]["type"] = "unknown";

#endif

        // ------------------------------------------------------------
        // Board
        // ------------------------------------------------------------

#ifdef BOARD_VARIANT
    doc["board"] = BOARD_VARIANT;
#else
    doc["board"] = "unknown";
#endif


    // ------------------------------------------------------------
    // JSON senden
    // ------------------------------------------------------------

    String response;
    serializeJson(doc, response);

    request->send(200, "application/json", response); });

    // Filament-Liste als JSON
    server.on("/filaments.json", HTTP_GET, [](AsyncWebServerRequest *request)
              {
        // FIX: network-load hint – file access + JSON
        LEDCTRL_FILAMENT::netBusyHint(350);
        LEDCTRL_NFC::netBusyHint(350);

        std::vector<FilamentEntry> list;
        FilamentDB::getAll(list);

        // Adjust document size based on the number of entries
        JsonDocument doc;
        JsonArray arr = doc.to<JsonArray>();

        for (auto &e : list) {
            JsonObject      o = arr.add<JsonObject>();
            o["uid"]        = e.uid;
            o["vendor"]     = e.vendor;
            o["type"]       = e.type;
            o["color"]      = e.color;
            o["ledIndex"]   = e.ledIndex;
            o["info1"]      = e.info1;
            o["info2"]      = e.info2;
            o["storage"]    = e.storage;
        }

        String json;
        serializeJson(arr, json);
        request->send(200, "application/json", json); });

    // --- api to export ALL (filaments + config) ---
    server.on("/api/exportAll", HTTP_GET, [](AsyncWebServerRequest *req)
              {
        // FIX: network-load hint – relatively large JSON response
        LEDCTRL_FILAMENT::netBusyHint(500);
        LEDCTRL_NFC::netBusyHint(500);

        JsonDocument outDoc;

        // config
        JsonObject cfg = outDoc["config"].to<JsonObject>();
        loadConfigAsJsonV2(cfg);

        // filaments
        JsonArray fils = outDoc["filaments"].to<JsonArray>();
        loadFilamentsAsJson(fils);

        String out;
        serializeJsonPretty(outDoc, out);
        req->send(200, "application/json", out); });

    // --- api to import ALL ---
    server.on("/api/importAll", HTTP_POST, [](AsyncWebServerRequest *req)
              { 
            // FIX: network-load hint – upload starts
            LEDCTRL_FILAMENT::netBusyHint(500);
            LEDCTRL_NFC::netBusyHint(500);
            req->send(200, "text/plain", "Upload started"); }, nullptr, [](AsyncWebServerRequest *req, uint8_t *data, size_t len, size_t index, size_t total)
              {
            // FIX: network-load hint – for every chunk
            LEDCTRL_FILAMENT::netBusyHint(500);
            LEDCTRL_NFC::netBusyHint(500);

            static String body;
            if (index == 0) { body = ""; if (total > 0) body.reserve(total); }
            body.concat((const char*)data, len);
            if (index + len != total) return;

            JsonDocument doc;
            DeserializationError err = deserializeJson(doc, body);
            if (err) {
                req->send(400, "text/plain", "JSON parse failed");
                if(CONFIGV2.system.debugMode) {
                    Serial.println("importAll JSON parse failed");
                }
                return;
            }

            if (doc["config"].is<JsonObject>())
                importConfigJsonV2(doc["config"].as<JsonObject>());

            if (doc["filaments"].is<JsonArray>())
                importFilamentsJson(doc["filaments"].as<JsonArray>());

            req->send(200, "text/plain", "Import OK"); });

    // Update single filament
    server.on("/api/update", HTTP_POST, [](AsyncWebServerRequest *req)
              {
            // FIX: network-load hint – short upload/JSON
            LEDCTRL_FILAMENT::netBusyHint(350);
            LEDCTRL_NFC::netBusyHint(350);
            req->send(200, "text/plain", "Processing"); }, nullptr, [](AsyncWebServerRequest *req, uint8_t *data, size_t len, size_t index, size_t total)
              {
            // FIX: network-load hint – per chunk
            LEDCTRL_FILAMENT::netBusyHint(350);
            LEDCTRL_NFC::netBusyHint(350);

            static String body;
            if(index == 0){
                body = "";
                if(total > 0) body.reserve(total);
            }
            body.concat((const char*)data, len);
            if(index + len != total) return;

            if(CONFIGV2.system.debugMode) {
                Serial.println("Update received: " + body);
            }

            JsonDocument doc;
            DeserializationError err = deserializeJson(doc, body);
            if(err){
                if(CONFIGV2.system.debugMode) {
                    Serial.print("update JSON parse failed: ");
                    Serial.println(err.c_str());
                }
                return;
            }

            // Read the index from JSON
            int idx = doc["idx"] | -1;
            if(idx < 0){
                if(CONFIGV2.system.debugMode) {
                    Serial.println("Update failed: missing index");
                }
                return;
            }

            FilamentEntry entry;
            entry.uid       = doc["uid"].as<String>();
            entry.vendor    = doc["vendor"].as<String>();
            entry.type      = doc["type"].as<String>();
            entry.color     = doc["color"].as<String>();
            entry.ledIndex  = doc["ledIndex"].as<int>();
            entry.info1     = doc["info1"].as<String>();
            entry.info2     = doc["info2"].as<String>();
            entry.storage   = doc["storage"].as<String>();

            // Update by index
            if(FilamentDB::updateAtIndex(idx, entry)){
                saveFilamentsToFile();
                if(CONFIGV2.system.debugMode) {
                    Serial.println("DB updated and saved");
                }
            } else {
                if(CONFIGV2.system.debugMode) {
                    Serial.println("DB update failed");
                }
            } });

    // Add a new entry
    server.on("/api/add", HTTP_POST, [](AsyncWebServerRequest *req)
              {
            // FIX: network-load hint – short upload/JSON
            LEDCTRL_FILAMENT::netBusyHint(350);
            LEDCTRL_NFC::netBusyHint(350);
            req->send(200, "text/plain", "Processing"); }, nullptr, [](AsyncWebServerRequest *req, uint8_t *data, size_t len, size_t index, size_t total)
              {
            // FIX: network-load hint – per chunk
            LEDCTRL_FILAMENT::netBusyHint(350);
            LEDCTRL_NFC::netBusyHint(350);

            static String body;
            if (index == 0) {
                body = "";
                if (total > 0) body.reserve(total);
            }
            body.concat((const char*)data, len);
            if (index + len != total) return;

            JsonDocument doc;

            DeserializationError err = deserializeJson(doc, body);
            if (err) {
                if(CONFIGV2.system.debugMode) {
                    Serial.print("ADD: JSON parse failed: ");
                    Serial.println(err.c_str());
                }
                return;
            }

            FilamentEntry entry;
            entry.uid       = doc["uid"].as<String>();
            entry.vendor    = doc["vendor"].as<String>();
            entry.type      = doc["type"].as<String>();
            entry.color     = doc["color"].as<String>();
            entry.ledIndex  = doc["ledIndex"].as<int>();
            entry.info1     = doc["info1"].as<String>();
            entry.info2     = doc["info2"].as<String>();
            entry.storage   = doc["storage"].as<String>();

            if (FilamentDB::add(entry)) {
                if(CONFIGV2.system.debugMode) {
                    Serial.println("ADD filament: OK");
                }
                saveFilamentsToFile();
            } else {
                if(CONFIGV2.system.debugMode) {
                    Serial.println("ADD filament: FAILED");
                }
            } });

    server.on("/api/delete", HTTP_POST, [](AsyncWebServerRequest *request)
              {
        // FIX: network-load hint – small JSON response + DB access
        LEDCTRL_FILAMENT::netBusyHint(250);
        LEDCTRL_NFC::netBusyHint(250);

        if (!request->hasParam("uid", true)) {
            request->send(400, "application/json",
                "{\"status\":\"error\",\"msg\":\"missing uid\"}");
            return;
        }

        String uid = request->getParam("uid", true)->value();

        if (!FilamentDB::remove(uid)) {
            request->send(404, "application/json",
                "{\"status\":\"error\",\"msg\":\"uid not found\"}");
            return;
        } else {
            saveFilamentsToFile();
        }

        request->send(200, "application/json", "{\"status\":\"ok\"}"); });

    // Config als JSON ausliefern
    server.on("/config_v2.json", HTTP_GET, [](AsyncWebServerRequest *request)
              {
        // FIX: network-load hint – FS read + JSON
        LEDCTRL_FILAMENT::netBusyHint(250);
        LEDCTRL_NFC::netBusyHint(250);

        if (!LittleFS.exists("/config_v2.json")) {
            request->send(404, "application/json", "{\"error\":\"config_v2.json missing\"}");
            return;
        }
        request->send(LittleFS, "/config_v2.json", "application/json"); });

    // server.on("/logo.png", HTTP_GET, ...);    // entfernt
    // server.on("/favicon.ico", HTTP_GET, ...); // entfernt

    // Update LED config (safer upload handler)
    server.on("/api/updateConfig", HTTP_POST, [](AsyncWebServerRequest *req)
              { 
            // FIX: network-load hint – start of config upload
            LEDCTRL_FILAMENT::netBusyHint(400);
            LEDCTRL_NFC::netBusyHint(400); },     // no GET handler needed
              nullptr, // no body-upload handler for chunked POST
              [](AsyncWebServerRequest *req, uint8_t *data, size_t len, size_t index, size_t total)
              {
            // FIX: network-load hint – per chunk
            LEDCTRL_FILAMENT::netBusyHint(400);
            LEDCTRL_NFC::netBusyHint(400);

            static String body;
            if (index == 0) {
                body = "";
                if (total > 0) body.reserve(total);
            }
            body.concat((const char*)data, len);

            if (index + len != total) return; // noch nicht alles empfangen

            // --- JSON parsen ---
            JsonDocument doc;
            DeserializationError err = deserializeJson(doc, body);

            
            
            if (err) {
                req->send(400, "text/plain", "JSON Error");
                if(CONFIGV2.system.debugMode) {
                    Serial.print("updateConfig JSON error: ");
                    Serial.println(err.c_str());
                }
                return;
            }       

            // --- Update CONFIG ---
            if (!updateConfigFromJsonV2(doc)) {
                req->send(400, "text/plain", "Invalid JSON structure");
                return;
            }

            req->send(200, "application/json", "{\"status\":\"ok\"}"); });

    server.on("/api/reboot", HTTP_POST, [](AsyncWebServerRequest *request)
              {
        // FIX: network-load hint – process request
        LEDCTRL_FILAMENT::netBusyHint(250);
        LEDCTRL_NFC::netBusyHint(250);

        const unsigned long nowMs = millis();

        if (!rebootPending) {
            // Akustik + Countdown starten
            buzzer_double_beep();
            rebootPending = true;
            rebootAt      = nowMs + REBOOT_DELAY_WEBIF_MS;

            // Button-States flushen, damit kein sofortiges Cancel aus altem Zustand kommt
            gpiohw_reset_click_state();

            // IMPORTANT: immediately arm the LEDs + UI (idempotent)
            // FIX: compile-safe thanks to the forward declaration above
            renderRebootCountdown(nowMs);
        }
        // optional: return status JSON
        request->send(200, "application/json", "{\"status\":\"ok\",\"pending\":true}"); });

    server.on("/api/otaUpdate", HTTP_POST, [](AsyncWebServerRequest *req)
              {
        if (otaAborted) {
            req->send(409, "application/json",
                "{\"status\":\"error\",\"msg\":\"Update aborted\"}");
        } else {
            req->send(200, "text/plain", "Upload started");
        }
        otaAborted = false; }, nullptr, [](AsyncWebServerRequest *req, uint8_t *data, size_t len, size_t index, size_t total)
              {

        if (otaAborted) return; // weitere Chunks ignorieren

        SysInfo info = getSysInfo();

        if (req->hasParam("filename", true)) {
            String fname = req->getParam("filename", true)->value();
            if (!fname.startsWith("firmware") || !fname.endsWith(".bin")) {
                req->send(400, "text/plain", "Wrong filename! Must start with 'firmware' and end with '.bin'");
                otaAborted = true;
                return;
            }
        }

        if (index == 0) {
            Serial.printf("Starting FW OTA update: %u bytes\n", total);

            // --- Chip-Vorab-Check, BEVOR irgendetwas geflasht wird ---
            if (len < 16 || data[0] != 0xE9) {
                Serial.println("Invalid image: bad magic byte");
                MYDISPLAY::showThreeLinesCentered(F("Ungueltige"), F("FW-Datei"), F(""));
                req->send(400, "application/json",
                    "{\"status\":\"error\",\"msg\":\"Kein gueltiges Firmware-Image\"}");
                otaAborted = true;
                return;
            }

            uint16_t imgChip = data[12] | (data[13] << 8);
            uint16_t myChip  = runningChipId();

            if (CONFIGV2.system.debugMode) {
                Serial.printf("Header check: imgChip=%u (0x%04X), myChip=%u (0x%04X)\n",
                              imgChip, imgChip, myChip, myChip);
            }

            if (imgChip != myChip) {
                String msg = "FW fuer " + chipIdToName(imgChip) +
                             ", Board ist " + chipIdToName(myChip);
                Serial.println(msg);

                DisplayAnim::stop();
                MYDISPLAY::showThreeLinesCentered(
                    F("Falsche FW!"),
                    chipIdToName(imgChip),
                    F("erwartet")
                );
                LEDCTRL_NFC::showError();        // NFC-Ring sofort rot (solid)
                LEDCTRL_FILAMENT::errorBlink();  // Filament: blinks -> red (as desired)

                req->send(409, "application/json",
                    "{\"status\":\"error\",\"msg\":\"" + msg + "\"}");
                otaAborted = true;
                return;
            }

            DisplayAnim::stop();
            MYDISPLAY::showThreeLinesCentered(F("started"), F("FW"), F("update"));

            if (!Update.begin(total)) {
                Serial.println("OTA begin failed");
                MYDISPLAY::showThreeLinesCentered(F("FW OTA"), F("update"), F("failed"));
                LEDCTRL_NFC::showError();        // NFC-Ring sofort rot (solid)
                LEDCTRL_FILAMENT::errorAll();  // Filament: red (as desired)
                req->send(500, "application/json",
                    "{\"status\":\"error\",\"msg\":\"Update.begin failed\"}");
                otaAborted = true;
                return;
            }
        }

        if (Update.write(data, len) != len) {
            Serial.printf("FW update write failed! Error: %d\n", Update.getError());
            MYDISPLAY::showThreeLinesCentered(F("FW OTA"), F("update"), F("failed"));
            LEDCTRL_NFC::showError();        // NFC-Ring sofort rot (solid)
            LEDCTRL_FILAMENT::errorAll();  // Filament: red (as desired)
            req->send(500, "application/json",
                "{\"status\":\"error\",\"msg\":\"Write failed\"}");
            otaAborted = true;
            return;
        }

        if (index + len == total) {
            if (Update.end(false)) {
                Serial.println("FW OTA applied successfully");
                MYDISPLAY::showThreeLinesCentered(F("FW OTA"), F("update"), F("success"));
                LEDCTRL_FILAMENT::successAll();  // Filament: green (as desired)
                req->send(200, "application/json",
                    "{\"status\":\"ok\",\"msg\":\"FW update successful, rebooting\"}");
                
                rebootReason = true; // true = success
                rebootPending = true;
                rebootAt = millis() + 1000;
                
            } else {
                Serial.printf("Update.end failed! Error: %d\n", Update.getError());
                MYDISPLAY::showThreeLinesCentered(F("FW OTA"), F("update"), F("failed"));
                LEDCTRL_FILAMENT::errorAll();  // Filament: red (as desired)
                req->send(500, "application/json",
                    "{\"status\":\"error\",\"msg\":\"FW update failed\"}");
            }
        } });

    server.on("/api/selfUpdate", HTTP_POST, [](AsyncWebServerRequest *req)
              {
    if (startSelfUpdate()) {
        req->send(200, "application/json",
            "{\"status\":\"ok\",\"msg\":\"Firmware update started\"}");
            DisplayAnim::stop();
            MYDISPLAY::showThreeLinesCentered(F("FW update"), F("started"), F("0%"));
    } else {
        req->send(500, "application/json",
            "{\"status\":\"error\",\"msg\":\"Firmware update could not be started\"}");
            MYDISPLAY::showThreeLinesCentered(F("FW update"), F("failed"), F("pls reboot"));
            LEDCTRL_NFC::showError();        // NFC-Ring sofort rot (solid)
            LEDCTRL_FILAMENT::errorAll();  // Filament: red (as desired)
    } });

    server.on("/api/filamanSync", HTTP_POST, [](AsyncWebServerRequest *req)
              {
                  if (CONFIGV2.system.debugMode)
                  {
                      Serial.println("[API] request filaman sync");
                  }

                  bool started = FilamanManager::requestSync();

                  JsonDocument doc;
                  doc["started"] = started;
                  String out;
                  serializeJson(doc, out);
                  req->send(started ? 200 : 409, "application/json", out); // 409 = schon busy/disabled
              });

    server.on("/api/factoryReset", HTTP_POST, [](AsyncWebServerRequest *request)
              {
                request->send(200, "application/json", "{\"success\":true}");

                factoryResetRequested = true; });

                server.begin();
            }

void sendHeartbeat(AsyncWebSocket &ws)
{
    unsigned long now = millis();
    if (now - lastHeartbeatMs < HEARTBEAT_INTERVAL_MS)
        return;
    lastHeartbeatMs = now;

    JsonDocument doc;
    doc["action"] = "heartbeat";
    doc["uptime_ms"] = millis();
    doc["heap_free"] = ESP.getFreeHeap();
    doc["wifi_rssi"] = WiFi.RSSI();
    doc["cpu_temp_c"] = temperatureRead();

    if (CONFIGV2.filamanConfig.enabled)
    {
        doc["filamanSync"] = FilamanManager::isSyncBusy();
    }

    // Update-Info
    UpdateInfo &update = getUpdateInfo();

    // send info update availabl eonly if available, otherwise just send updateAvailable=false
    if (update.updateAvailable)
    {
        doc["updateAvailable"] = update.updateAvailable;
        doc["currentVersion"] = update.currentVersion;
        doc["latestVersion"] = update.latestVersion;
        doc["lastCheck"] = update.lastCheck;
    }
    else
    {
        doc["updateAvailable"] = false;
    }

    // request self-update status
    SelfUpdateStatus &selfUpdate = getSelfUpdateStatus();

    // send self-update info only if running or finished, otherwise just send selfUpdate=false
    if (selfUpdate.running || selfUpdate.finished)
    {
        doc["selfUpdate"] = true;
        doc["selfUpdateRunning"] = selfUpdate.running;
        doc["selfUpdateFinished"] = selfUpdate.finished;
        doc["selfUpdateSuccess"] = selfUpdate.success;
        doc["selfUpdateProgress"] = selfUpdate.progress;
        doc["selfUpdateMessage"] = selfUpdate.message;
    }
    else
    {
        doc["selfUpdate"] = false;
    }

    String out;
    serializeJson(doc, out);
    ws.textAll(out); // an alle Clients senden
}

void sendStorageLocation(AsyncWebSocket &ws, String location)
{
    JsonDocument doc;
    doc["storageLocation"] = location;
    String out;
    serializeJson(doc, out);
    ws.textAll(out);
}
