mark77-DE/Smart-Filament-Sample-Board/ESP32-Webserver/src/display/st7789/display_st7789.cpp

#include "display/display_config.h"

#if DISPLAY_TYPE == DISPLAY_TYPE_ST7789

#include "display/st7789/display_st7789.h"  // LGFX bekannt
#include "display/display.h"

#include <SPI.h>

#include <LovyanGFX.hpp>


DisplayType display;

void displayInit() {
    display.init();
    display.setBrightness(255);
    display.setRotation(1);

    display.fillScreen(TFT_BLACK);
    
    display.setTextColor(TFT_WHITE, TFT_BLACK);
    display.setTextSize(1);

    MYDISPLAY::init(&display);

    display.fillScreen(TFT_BLACK);
    display.setTextDatum(MC_DATUM);
    display.setTextColor(TFT_WHITE);
    display.setTextSize(2);

    const int cx = display.width() / 2;
    const int cy = display.height() / 2;

    // display.drawString("DISPLAY OK", cx, cy);

    // delay(2000);
}

void displayClear() { display.fillScreen(0); }
void displayFlush() { /* TFT braucht kein flush */ }
void displayLoop() {}

void displayShowIP(const String &ip) {
    display.fillScreen(TFT_BLACK);
    display.setTextDatum(MC_DATUM);
    display.setTextSize(2);
    display.setTextColor(TFT_GREEN);

    const int cx = display.width() / 2;
    const int cy = display.height() / 2;

    display.drawString(ip.c_str(), cx, cy);
}

int MYDISPLAY::getMaxTextSize(const String& text, int maxWidth, int maxSize) {
    if (!_display) return 1;

    int best = 1;

    for (int s = 1; s <= maxSize; s++) {
        _display->setTextSize(s);
        if (_display->textWidth(text) > maxWidth) break;
        best = s;
    }

    return best;
}


void MYDISPLAY::clear() {
    if (_display) _display->fillScreen(TFT_BLACK);
}

void MYDISPLAY::showThreeLinesCentered(
    const String& line1,
    const String& line2,
    const String& line3,
    int foregroundColor,
    int backgroundColor
) {
    if (!_display) return;

    _display->fillScreen(TFT_BLACK);
    _display->setTextDatum(MC_DATUM);
    _display->setTextColor(foregroundColor, backgroundColor);
    _display->setTextSize(2);

    const int cx = display.width() / 2;
    const int cy = display.height() / 2;

    const int lineSpacing = display.height() / 6;

    _display->drawString(line1, cx, cy - lineSpacing);
    _display->drawString(line2, cx, cy);
    _display->drawString(line3, cx, cy + lineSpacing);
}



void MYDISPLAY::showFourLinesCentered(
    const String& line1,
    const String& line2,
    const String& line3,
    const String& line4
) {
    if (!_display) return;

    _display->fillScreen(TFT_BLACK);
    _display->setTextDatum(TL_DATUM);

    const int w = _display->width();
    const int h = _display->height();
    const int cx = w / 2;

    _display->setTextSize(1);

    // ---------- Calculate heights ----------
    int y1 = h * 0.15;
    int y2 = h * 0.35;
    int y3 = h * 0.60;
    int y4 = h * 0.85;

    // ---------- LINE 1 ----------
    _display->setFont(&fonts::Font4);
    int tw = _display->textWidth(line1);
    _display->setTextColor(TFT_WHITE, TFT_BLACK);
    _display->drawString(line1, cx - (tw / 2), y1);

    _display->drawLine(0, y1 + 20, w, y1 + 20, TFT_CYAN);

    // ---------- LINE 2 ----------
    _display->setFont(&fonts::Font4);
    tw = _display->textWidth(line2);
    _display->setTextColor(TFT_WHITE, TFT_BLACK);
    _display->drawString(line2, cx - (tw / 2), y2);

    // ---------- LINE 3 ----------
    _display->setFont(&fonts::Font4);
    tw = _display->textWidth(line3);
    _display->setTextColor(TFT_LIGHTGREY, TFT_BLACK);
    _display->drawString(line3, cx - (tw / 2), y3);

    // ---------- LINE 4 ----------
    _display->setFont(&fonts::Font4);
    tw = _display->textWidth(line4);
    _display->setTextColor(TFT_LIGHTGREY, TFT_BLACK);
    _display->drawString(line4, cx - (tw / 2), y4);

    //reset Font
    _display->setFont(nullptr);
}

void MYDISPLAY::showCentered(
    const String& msg,
    const int FOREGROUND_COLOR,
    const int BACKGROUND_COLOR
) {
    if (!_display) return;

    _display->fillScreen(TFT_BLACK);
    _display->setTextDatum(MC_DATUM);
    _display->setTextColor(FOREGROUND_COLOR, BACKGROUND_COLOR);
    _display->setTextSize(3);

    const int cx = display.width() / 2;
    const int cy = display.height() / 2;

    _display->drawString(msg.c_str(), cx, cy);
}

void MYDISPLAY::showBootVersion(const char* version, const char* dateShort) {
    if (!_display) return;

    _display->fillScreen(TFT_BLACK);
    _display->setTextDatum(MC_DATUM);
    _display->setTextColor(TFT_WHITE, TFT_BLACK);
    _display->setTextSize(2);

    const int cx = display.width() / 2;
    const int cy = display.height() / 2;

    const int offset = display.height() / 8;

    _display->drawString(version, cx, cy - offset);
    _display->drawString(dateShort, cx, cy + offset);
}



void MYDISPLAY::showErrorCentered(
    const String& msg,
    const int FOREGROUND_COLOR,
    const int BACKGROUND_COLOR
) {
    if (!_display) return;

    _display->fillScreen(TFT_BLACK);
    _display->setTextDatum(MC_DATUM);
    _display->setTextColor(FOREGROUND_COLOR, BACKGROUND_COLOR);
    _display->setTextSize(3);

    const int cx = display.width() / 2;
    const int cy = display.height() / 2;

    _display->drawString(msg.c_str(), cx, cy);

    

    // ----------------------
    // 2px breiter roter Rahmen
    // ----------------------
    const int borderWidth = 2;
    _display->drawRect(
        borderWidth / 2,                        // x = 1 (2px Rand innen)
        borderWidth / 2,                        // y = 1
        _display->width() - borderWidth,        // Breite
        _display->height() - borderWidth,       // Height
        FOREGROUND_COLOR                        // Farbe
    );
}


// display_oled.cpp
namespace {
    bool s_selfUpdateActive = false;   // merkt sich, ob wir gerade "im Update-Modus" sind
}

void MYDISPLAY::renderSelfUpdateStatus(const SelfUpdateStatus& status) {

    
}


// -----------------------------
// IMPORTANT: definition of the static members
// -----------------------------
DisplayType* MYDISPLAY::_display = nullptr;

#endif
