mark77-DE/Smart-Filament-Sample-Board/ESP32-S3-Filament-Webserver/data/admin.js

// -------------------- Globale Referenzen --------------------
const dbDiv = document.getElementById("db");
const addForm = document.getElementById("addForm");
const wsStatus = document.getElementById("wsStatus");
const editToggle = document.getElementById("editToggle");
const debugToggle = document.getElementById("debugToggle");

const ledPinSelect = document.getElementById("ledPin");
const nfcLedPinSelect = document.getElementById("nfcLedPin");

const ledBrightnessInput = document.getElementById("ledBrightness");
const nfcLedBrightnessInput = document.getElementById("nfcLedBrightness");

const maxLEDInput = document.getElementById("maxLED");
const nfcMaxLEDInput = document.getElementById("nfcMaxLED");

const ledColorInput = document.getElementById("ledColor");
const nfcLedColorSuccessInput = document.getElementById("nfcLedColorSuccess");
const nfcLedColorErrorInput = document.getElementById("nfcLedColorError");
const nfcLedColorPulseInput = document.getElementById("nfcLedColorPulse");

const ledTimeoutInput = document.getElementById("ledTimeout");
const nfcLedTimeoutInput = document.getElementById("nfcLedTimeout");

const nfcLedSuccessBlinkEnabledInput = document.getElementById("nfcLedSuccessBlinkEnabled");
const nfcLedSuccessBlinkCountInput   = document.getElementById("nfcLedSuccessBlinkCount");
const nfcLedSuccessBlinkMsInput      = document.getElementById("nfcLedSuccessBlinkMs");

const importFileInput = document.getElementById("importFile");
const importBtn = document.getElementById("importBtn");

let EDIT_MODE = false;
let CONFIG = null;
let lastHighlightedRow = null;


// -------------------- WebSocket --------------------

const ws = new WebSocket(`ws://${location.host}/ws`);

ws.onopen = () => updateWSStatus(true);
ws.onclose = () => {
    updateWSStatus(false);
    document.body.innerHTML = `
        <h2>ESP Verbindung verloren...</h2>
        <p>Seite wird in 5 Sekunden neu laden.</p>
    `;
    setTimeout(() => location.reload(), 5000);
};
ws.onerror = () => updateWSStatus(false);
ws.onmessage = handleWSMessage;



function hexToRgb(hex) {
    if (!hex || hex[0] !== '#' || hex.length !== 7) return [255, 0, 0]; // Default Rot
    const r = parseInt(hex.substr(1,2), 16);
    const g = parseInt(hex.substr(3,2), 16);
    const b = parseInt(hex.substr(5,2), 16);
    return [r, g, b];
}

function rgbToHex(rgb) {
    if (!Array.isArray(rgb) || rgb.length < 3) return "#ff0000"; // Default Rot
    const r = rgb[0].toString(16).padStart(2,'0');
    const g = rgb[1].toString(16).padStart(2,'0');
    const b = rgb[2].toString(16).padStart(2,'0');
    return `#${r}${g}${b}`;
}

function updateImportBtnVisibility() {
    importBtn.style.display = importFileInput.files.length ? "inline-block" : "none";
}



function updateWSStatus(connected){
    wsStatus.textContent = connected ? "WebSocket: verbunden" : "WebSocket: getrennt";
    wsStatus.classList.toggle("ws-connected", connected);
    wsStatus.classList.toggle("ws-disconnected", !connected);
}

// -------------------- Edit Mode --------------------
editToggle.addEventListener("change", () => {
    EDIT_MODE = editToggle.checked;
    applyEditMode();
});
function applyEditMode(){
    const table = document.querySelector("#table");
    if(!table) return;
    table.querySelectorAll(".tableRow").forEach(row => {
        row.querySelectorAll("span[contenteditable]").forEach(cell => cell.contentEditable = EDIT_MODE);
        row.querySelectorAll("select").forEach(sel => sel.disabled = !EDIT_MODE);
        row.querySelectorAll(".saveBtn, .deleteBtn").forEach(btn => EDIT_MODE ? btn.removeAttribute("hidden") : btn.setAttribute("hidden",""));
    });
}


// -------------------- WebSocket Handler --------------------
async function handleWSMessage(ev){
    let data;
    try { 
        data = JSON.parse(ev.data); 
    } catch (err) { 
        console.error("Fehler beim Parsen der WS-Daten:", ev.data, err);
        return; 
    }

    if(!data.uid) {
        //console.log("Keine UID im empfangenen Datenobjekt:", data);
        return;
    }

    // UID nur Hex-Ziffern, Großschreibung vereinheitlicht
    const scannedUID = data.uid.replace(/[^a-fA-F0-9]/g,'').toUpperCase();
    //console.log("Scanned UID:", scannedUID);

    const rows = document.querySelectorAll("#db .tableRow");
    let highlighted = false;

    rows.forEach((row, idx) => {
        const uidCell = row.querySelector(".uid");
        if (!uidCell) {
            //console.log("Keine UID-Zelle in Zeile", idx);
            return;
        }

        const rowUID = uidCell.textContent.replace(/[^a-fA-F0-9]/g,'').toUpperCase();
        //console.log(`Zeile ${idx}: rowUID=${rowUID} | scannedUID=${scannedUID}`);

        if (rowUID === scannedUID) {
            //console.log(`Zeile ${idx} match!`);
            highlighted = true;

            if (lastHighlightedRow && lastHighlightedRow !== row) {
                //console.log("Entferne vorherige Highlight-Markierung von Zeile", lastHighlightedRow.dataset.idx);
                lastHighlightedRow.classList.remove("highlight");
            }

            row.classList.add("highlight");
            lastHighlightedRow = row;

            row.scrollIntoView({ behavior: "smooth", block: "center" });
        }
    });

    if (!highlighted) {
        //console.log("UID unbekannt, Add-Form vorbereiten:", scannedUID);
        document.querySelector('#addForm input[name="uid"]').value = data.uid;
        document.querySelector('#addForm input[name="vendor"]').focus();

        if(lastHighlightedRow) lastHighlightedRow.classList.remove("highlight");
        lastHighlightedRow = null;
    }
}






// -------------------- Export / Import --------------------
document.getElementById("exportAllBtn").addEventListener("click", async () => {
    try {
        const res = await fetch("/api/exportAll");
        if (!res.ok) throw new Error("Export fehlgeschlagen");

        const blob = await res.blob();
        const url = URL.createObjectURL(blob);

        // Zeitstempel erzeugen
        const now = new Date();
        const pad = (n) => n.toString().padStart(2, "0");
        const timestamp = `${now.getFullYear()}${pad(now.getMonth()+1)}${pad(now.getDate())}_${pad(now.getHours())}${pad(now.getMinutes())}${pad(now.getSeconds())}`;

        const a = document.createElement("a");
        a.href = url;
        a.download = `SpotMyFilament_Backup_${timestamp}.json`;
        document.body.appendChild(a);
        a.click();
        a.remove();
        URL.revokeObjectURL(url);
    } catch (err) {
        alert(err);
    }
});


document.getElementById("importAllForm").addEventListener("submit", async e=>{
    e.preventDefault();
    const fileInput = document.getElementById("importFile");
    if(!fileInput.files.length) return;
    const text = await fileInput.files[0].text();
    try{
        const res = await fetch("/api/importAll",{method:"POST",headers:{"Content-Type":"application/json"},body:text});
        if(res.ok){ alert("Import erfolgreich!"); CONFIG=null; await loadTable(); await updateAddFormLEDs(); }
        else { alert("Import fehlgeschlagen: "+await res.text()); }
    }catch(err){ alert("Import fehlgeschlagen: "+err); }
});
document.getElementById("importFile").addEventListener("change", e=>{
    document.getElementById("uploadLabel").textContent = e.target.files.length ? e.target.files[0].name : "Datei auswählen";
});

// -------------------- Reboot --------------------
document.getElementById("rebootBtn").addEventListener("click", async ()=>{
    if(!confirm("ESP wirklich neustarten?")) return;
    try{ await fetch("/api/reboot",{method:"POST"});} catch {}
    document.body.innerHTML="<h2>ESP wird neu gestartet...</h2><p>Bitte kurz warten.</p>";
});

// -------------------- Add Form --------------------
addForm.addEventListener("submit", async e=>{
    e.preventDefault();
    const fd = new FormData(addForm);
    const entry = {
        uid: fd.get("uid").trim(),
        vendor: fd.get("vendor").trim(),
        type: fd.get("type"),
        color: fd.get("color").trim(),
        ledIndex: Number(fd.get("ledIndex"))
    };
    const db = await (await fetch("/filaments.json")).json();
    const used = db.find(e=>Number(e.ledIndex)===entry.ledIndex);
    if(used){ alert(`LED ${entry.ledIndex + 1} bereits verwendet von UID ${used.uid}`); return; }
    const res = await fetch("/api/add",{method:"POST",headers:{"Content-Type":"application/json"},body:JSON.stringify(entry)});
    if(res.ok){ alert("Eintrag hinzugefügt!"); addForm.reset(); await loadTable(); await updateAddFormLEDs(); }
    else alert("Fehler beim Hinzufügen!");
});

// -------------------- Table / LED --------------------
async function loadTable() {
    await loadConfig();
    const res = await fetch("/filaments.json");
    if (!res.ok) {
        dbDiv.innerHTML = "<p>Fehler beim Laden der Daten.</p>";
        return;
    }

    const data = await res.json();
    const usedLEDs = new Set(data.map(e => Number(e.ledIndex)));

    let html = `
        <div id="table">
            <div id="tableHeader">
                <span id="uidHeader">Tag UID</span>
                <span id="vendorHeader">Name</span>
                <span id="typeHeader">Typ</span>
                <span id="colorHeader">Farbe</span>
                <span id="ledHeader">LED</span>
                <span id="actionHeader">Aktion</span>
            </div>
    `;

    //data.forEach((e, idx) => console.log(idx, e.uid));

    data.forEach((e, idx) => {
        html += `
            <div class="tableRow">
                <span class="uid" contenteditable="${EDIT_MODE}" data-field="uid" data-idx="${idx}">${e.uid}</span>
                <span class="vendor" contenteditable="${EDIT_MODE}" data-field="vendor" data-idx="${idx}">${e.vendor}</span>
                <span class="type" data-idx="${idx}">
                    <select data-field="type" ${EDIT_MODE ? "" : "disabled"}>
                        ${getTypeOptions(e.type)}
                    </select>
                </span>
                <span class="color" contenteditable="${EDIT_MODE}" data-field="color" data-idx="${idx}">${e.color}</span>
                <span class="led" data-idx="${idx}">
                    ${buildLedDropdown(Number(e.ledIndex), usedLEDs, !EDIT_MODE)}
                </span>
                <div class="actionCell">
                    <button class="saveBtn" data-idx="${idx}" ${EDIT_MODE ? "" : "hidden"}>Speichern</button>
                    <button class="deleteBtn" data-uid="${e.uid}" ${EDIT_MODE ? "" : "hidden"}>Löschen</button>
                </div>
            </div>
        `;
    });

    html += "</div>";
    dbDiv.innerHTML = html;

    activateButtons();
    applyEditMode(); // Buttons / selects im Edit-Modus korrekt setzen

    debugToggle.checked = CONFIG.options.debugMode || false;

    ledPinSelect.value = CONFIG.options.ledPin;
    nfcLedPinSelect.value = CONFIG.options.nfcLedPin;

    ledBrightnessInput.value = ledValueToPercent(CONFIG.options.ledBrightness);
    nfcLedBrightnessInput.value = ledValueToPercent(CONFIG.options.nfcLedBrightness);

    maxLEDInput.value = CONFIG.options.ledCount;
    nfcMaxLEDInput.value = CONFIG.options.nfcLedCount;

    ledTimeoutInput.value = CONFIG.options.ledTimeout;
    nfcLedTimeoutInput.value = CONFIG.options.nfcLedTimeout;

    ledColorInput.value = rgbToHex(CONFIG.options.ledColor);
    nfcLedColorSuccessInput.value = rgbToHex(CONFIG.options.nfcLedColorSuccess);
    nfcLedColorErrorInput.value = rgbToHex(CONFIG.options.nfcLedColorError);
    nfcLedColorPulseInput.value = rgbToHex(CONFIG.options.nfcLedColorPulse);

    // --- Success Blink UI ---
    nfcLedSuccessBlinkEnabledInput.checked = CONFIG.options.nfcLedSuccessBlinkEnabled ?? true;
    nfcLedSuccessBlinkCountInput.value     = CONFIG.options.nfcLedSuccessBlinkCount   ?? 3;
    nfcLedSuccessBlinkMsInput.value        = CONFIG.options.nfcLedSuccessBlinkMs      ?? 150;

    const syncBlinkUi = () => {
        const en = !!nfcLedSuccessBlinkEnabledInput.checked;
        nfcLedSuccessBlinkCountInput.disabled = !en;
        nfcLedSuccessBlinkMsInput.disabled    = !en;
    };
    nfcLedSuccessBlinkEnabledInput.onchange = syncBlinkUi;
    syncBlinkUi();

    
}


function getTypeOptions(selected){ return ["PLA","PLA+","PLA-CF","PLA-Matte","PETG","PETG-CF","ABS","ASA","TPU","Nylon","Holz"].map(t=>`<option value="${t}" ${t===selected?"selected":""}>${t}</option>`).join(""); }

function buildLedDropdown(currentLED, usedLEDs, disabled=false) {
    let html = `<select data-field="ledIndex" ${disabled ? "disabled" : ""}>`;
    for (let i = 0; i < CONFIG.options.ledCount; i++) {
        if (!usedLEDs.has(i) || i === currentLED) {
            html += `<option value="${i}" ${i === currentLED ? "selected" : ""}>LED ${i+1}</option>`;
        }
    }
    html += `</select>`;
    return html;
}


// -------------------- Buttons für Save/Delete --------------------
function activateButtons(){
    document.querySelectorAll(".saveBtn").forEach(btn=>btn.addEventListener("click", async ()=>{
        if(!confirm("Eintrag sichern?")) return;
        const idx=Number(btn.dataset.idx); const row=btn.closest(".tableRow");
        const entry={idx};
        row.querySelectorAll("[data-field]").forEach(el=>{
            const field=el.dataset.field;
            entry[field]=el.tagName==="SELECT"?el.value:el.innerText.trim();
        });
        const res=await fetch("/api/update",{method:"POST",headers:{"Content-Type":"application/json"},body:JSON.stringify(entry)});
        if(res.ok){ alert("Eintrag gespeichert!"); await loadTable(); await updateAddFormLEDs(); } else alert("Fehler beim Speichern!");
    }));

    document.querySelectorAll(".deleteBtn").forEach(btn => btn.addEventListener("click", async () => {
    if(!confirm("Eintrag wirklich löschen?")) return;

    const uid = btn.dataset.uid;
    const res = await fetch("/api/delete", {
        method: "POST",
        headers: { "Content-Type": "application/x-www-form-urlencoded" },
        body: `uid=${encodeURIComponent(uid)}`
    });

    if(res.ok){ alert("Eintrag gelöscht!"); await loadTable(); await updateAddFormLEDs(); }
    else alert("Fehler beim Löschen!");
}));
}


async function updateAddFormLEDs(){ 
    const data=await (await fetch("/filaments.json")).json(); 
    const free=[]; 
        for(let i=0;i<CONFIG.options.ledCount;i++)
            { if(!data.find(e=>Number(e.ledIndex)===i)) free.push(i); } 
        const sel=document.getElementById("ledIndexSelect"); 
        sel.innerHTML=""; 
        free.forEach(v=>{ const opt=document.createElement("option"); 
            opt.value = v; 
            opt.textContent = `LED ${v+1}`; 
            sel.appendChild(opt); }); 
        
}

// -------------------- LED Config --------------------
document.getElementById("saveConfig").addEventListener("click", async () => {
    if(!confirm("Konfiguration sichern?")) return;
    const ledCount = Number(document.getElementById("maxLED").value);
    const ledPin = Number(document.getElementById("ledPin").value);
    const ledBrightness = percentToLedValue(Number(document.getElementById("ledBrightness").value));
    const ledColor = hexToRgb(document.getElementById("ledColor").value);
    const ledTimeout = Number(document.getElementById("ledTimeout").value);

    const debugMode = debugToggle.checked;



    const nfcLedCount = Number(document.getElementById("nfcMaxLED").value);
    const nfcLedPin = Number(document.getElementById("nfcLedPin").value);
    const nfcLedBrightness = percentToLedValue(Number(document.getElementById("nfcLedBrightness").value));
    const nfcLedColorSuccess = hexToRgb(document.getElementById("nfcLedColorSuccess").value);
    const nfcLedColorError = hexToRgb(document.getElementById("nfcLedColorError").value);
    const nfcLedTimeout = Number(document.getElementById("nfcLedTimeout").value);
    const nfcLedColorPulse = hexToRgb(document.getElementById("nfcLedColorPulse").value);
    const nfcLedSuccessBlinkEnabled = document.getElementById("nfcLedSuccessBlinkEnabled").checked;
    const nfcLedSuccessBlinkCount   = Number(document.getElementById("nfcLedSuccessBlinkCount").value);
    const nfcLedSuccessBlinkMs      = Number(document.getElementById("nfcLedSuccessBlinkMs").value);


    if(debugMode) {
        console.log("Neue LED Config:", {
            ledCount, ledPin, ledBrightness, ledColor, ledTimeout,
            nfcLedCount, nfcLedPin, nfcLedBrightness, nfcLedColorSuccess, nfcLedColorError, nfcLedTimeout,
            debugMode
        });
    }


       
    try {
        await fetch("/api/updateConfig", {
    method: "POST",
    headers: { "Content-Type": "application/json" },
    body: JSON.stringify({
        options: {
            ledCount,
            ledPin,
            ledBrightness,
            ledColor,
            ledTimeout,

            nfcLedCount,
            nfcLedPin,
            nfcLedBrightness,
            nfcLedColorSuccess,
            nfcLedColorError,
            nfcLedColorPulse,
            nfcLedTimeout,

            nfcLedSuccessBlinkEnabled,
            nfcLedSuccessBlinkCount,
            nfcLedSuccessBlinkMs,

            debugMode
        }
    })
});

    } catch(e){
        // ESP schon offline – kein Problem
    }

   
});





// -------------------- LED / Config --------------------
async function loadConfig() {
    const res = await fetch("/config.json");
    if(!res.ok) throw new Error("Config konnte nicht geladen werden");
    const json = await res.json();

    CONFIG = json;
   
}



function updatePinOptions() {
    const ledPinValue = Number(ledPinSelect.value);
    const nfcPinValue = Number(nfcLedPinSelect.value);

    // Alle Optionen wieder aktivieren
    Array.from(ledPinSelect.options).forEach(opt => opt.disabled = false);
    Array.from(nfcLedPinSelect.options).forEach(opt => opt.disabled = false);

    // Pin vom jeweils anderen Dropdown deaktivieren
    nfcLedPinSelect.querySelectorAll(`option[value='${ledPinValue}']`).forEach(opt => opt.disabled = true);
    ledPinSelect.querySelectorAll(`option[value='${nfcPinValue}']`).forEach(opt => opt.disabled = true);
}

// Eventlistener hinzufügen
ledPinSelect.addEventListener("change", updatePinOptions);
nfcLedPinSelect.addEventListener("change", updatePinOptions);
importFileInput.addEventListener("change", updateImportBtnVisibility);


// -------------------- Color Presets (HEX) --------------------
const PRESET_COLORS = [
  "#ff0000", // Rot
  "#00ff00", // Grün
  "#0000ff", // Blau
  "#ffff00", // Gelb
  "#ff7a00", // Orange (schön satt)
  "#ff00ff", // Magenta
  "#00ffff"  // Cyan
];

function normalizeHex(v) {
  if (!v) return "";
  v = String(v).trim().toLowerCase();
  // nur exakt #RRGGBB akzeptieren
  return /^#([0-9a-f]{6})$/.test(v) ? v : "";
}

function autoFixHex(input) {
  let v = String(input.value).trim();

  // exakt 6 Hex-Zeichen ohne #
  if (/^[0-9a-fA-F]{6}$/.test(v)) {
    input.value = "#" + v.toLowerCase();
    return;
  }

  // # + 6 Hex-Zeichen → nur normalisieren
  if (/^#([0-9a-fA-F]{6})$/.test(v)) {
    input.value = v.toLowerCase();
  }
}


function clearActive(container) {
  container.querySelectorAll(".colorSwatch.active").forEach(el => el.classList.remove("active"));
}

function updateActiveForInput(container, input) {
  const current = normalizeHex(input.value);
  clearActive(container);

  if (!current) return; // ungültig => nichts markieren

  const match = container.querySelector(`.colorSwatch[data-hex="${current}"]`);
  if (match) match.classList.add("active"); // nur markieren, wenn es ein Preset ist
}

function initColorPresets() {
  document.querySelectorAll(".colorPresets").forEach((container) => {
    const targetId = container.dataset.target;
    const input = document.getElementById(targetId);
    if (!input) return;

    container.innerHTML = "";

    PRESET_COLORS.forEach((hex) => {
      const hexNorm = hex.toLowerCase();

      const sw = document.createElement("div");
      sw.className = "colorSwatch";
      sw.style.backgroundColor = hexNorm;
      sw.title = hexNorm;
      sw.dataset.hex = hexNorm;

      sw.addEventListener("click", () => {
        input.value = hexNorm;

        // Highlight setzen
        updateActiveForInput(container, input);

        // optional: Events triggern
        input.dispatchEvent(new Event("input", { bubbles: true }));
        input.dispatchEvent(new Event("change", { bubbles: true }));
      });

      container.appendChild(sw);
    });

        input.addEventListener("input", () => {
            autoFixHex(input);                
            updateActiveForInput(container, input);
        });

        input.addEventListener("change", () => {
            autoFixHex(input);                 
            updateActiveForInput(container, input);
        });


    // Initial markieren, falls Startwert ein Preset ist
    updateActiveForInput(container, input);
  });
}



function percentToLedValue(percent) {
    // clamp zwischen 0 und 100
    percent = Math.max(0, Math.min(100, percent));
    return Math.round((percent / 100) * 255);
}

function ledValueToPercent(value) {
    value = Math.max(0, Math.min(255, value));
    return Math.round((value / 255) * 100);
}



// -------------------- Init --------------------
async function init() {
    await loadConfig();
    await loadTable();
    await updateAddFormLEDs();
    updatePinOptions();
    updateImportBtnVisibility();
    initColorPresets();

    
}




init();
