mark77-DE/Smart-Filament-Sample-Board/ESP32-Webserver/src/globals.cpp

#include "globals.h"

volatile bool rebootPending = false;
unsigned long rebootAt      = 0;

uint32_t REBOOT_DELAY_MS       = 5000;  // Defaults
uint32_t REBOOT_DELAY_WEBIF_MS = 4000;

String LATEST_FIRMWARE_VERSION = "unknown";
